sixeight7/VController_v3/VC-mini hardware/Enclosure/VC-mini_lower_cover_b.png

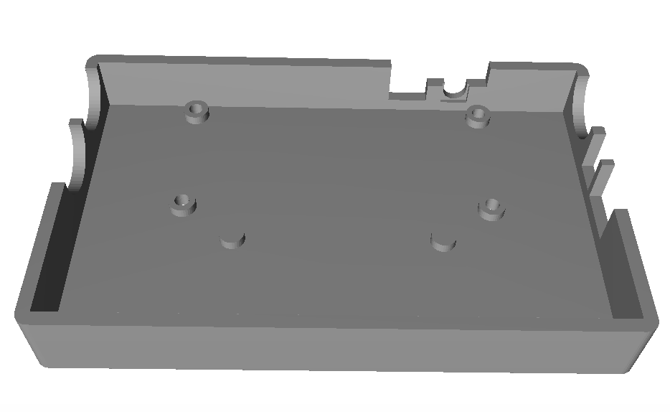
VC-mini hardware/Enclosure/VC-mini_lower_cover_b.png
