sixeight7/VController_v3/VC-touch hardware/Enclosure stl/vctouch_display_bezel.png

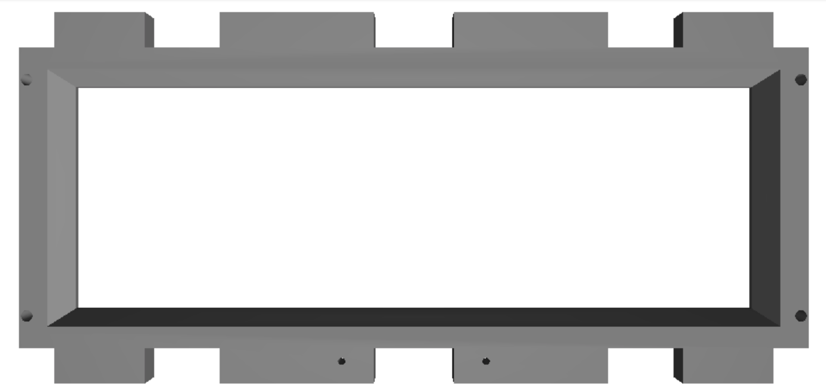
VC-touch hardware/Enclosure stl/vctouch_display_bezel.png
