sixeight7/VController_v3/VController hardware/Enclosure/RPi case/bottom part.png

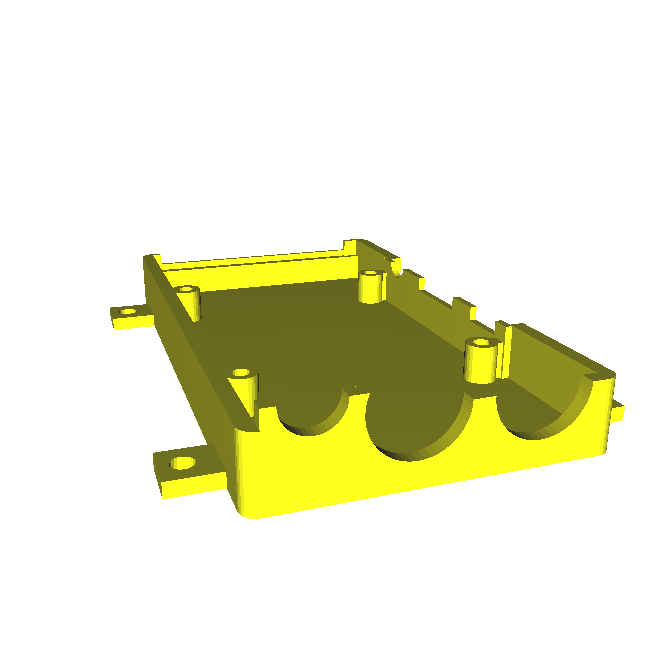
VController hardware/Enclosure/RPi case/bottom part.png
