sixeight7/VController_v3/VController hardware/Enclosure/RPi case/top part.png

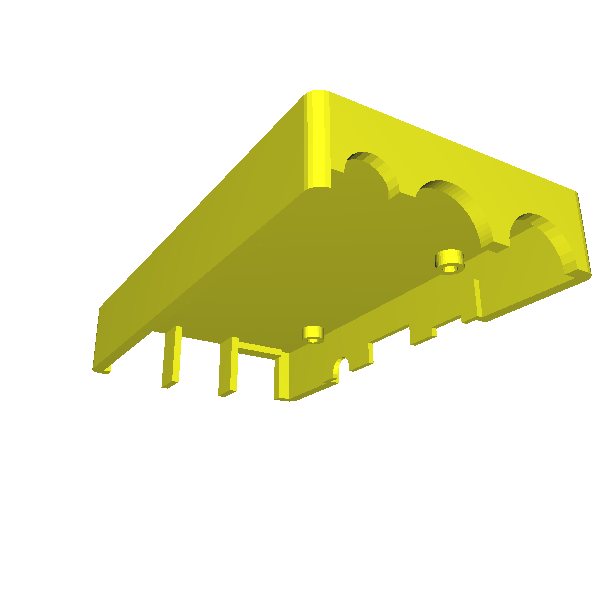
VController hardware/Enclosure/RPi case/top part.png
