sixeight7/VController_v3/VController hardware/Enclosure/3D printing/Large LCD support_2_0.stl

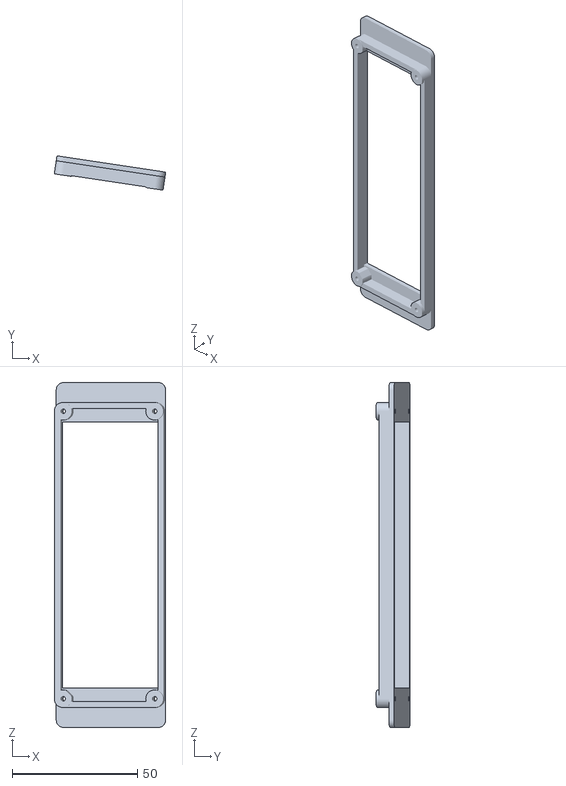
[picture p29: CAD file, 2017-03-23]
VController hardware/Enclosure/3D printing/Large LCD support_2_0.stl
44.6 x 13.7 x 138.0
