sixeight7/VController_v3/VController hardware/Enclosure/3D printing/Small 3xLCD support diameter_2_0.stl

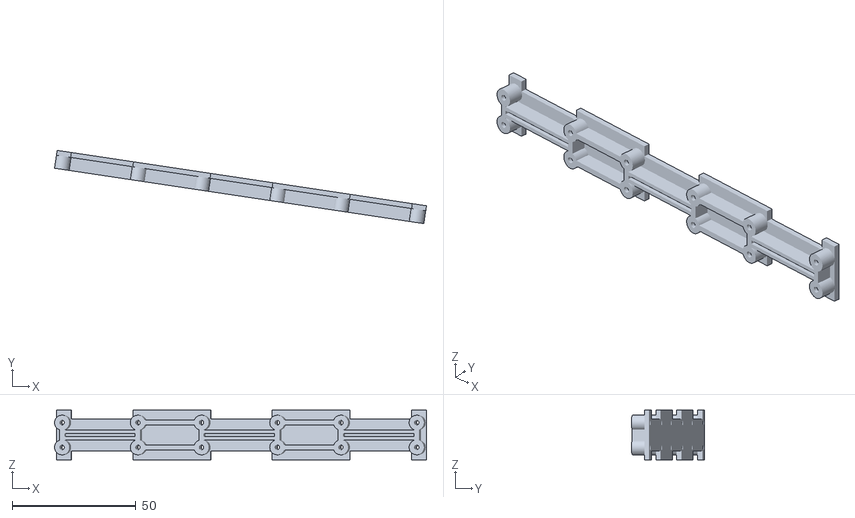
[picture p30: CAD file, 2017-03-23]
VController hardware/Enclosure/3D printing/Small 3xLCD support diameter_2_0.stl
150.4 x 29.6 x 20.2
