sixeight7/VController_v3/VController hardware/Enclosure/Metal/VController_mk4.step

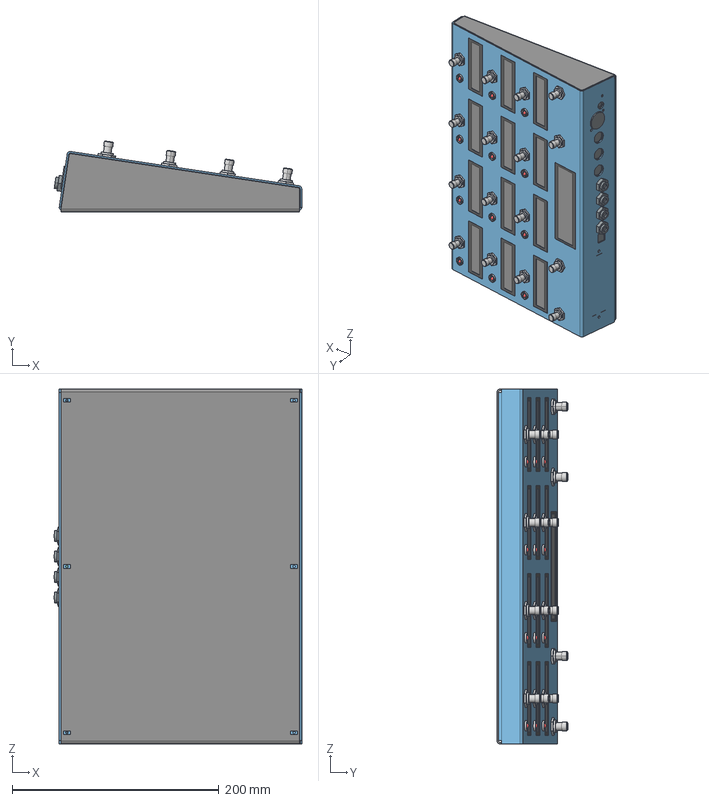
[picture p31: CAD file, 2017-03-23]
VController hardware/Enclosure/Metal/VController_mk4.step
239.2 x 68.7 x 343.0 mm
bracket
rpi_print
LED.9 x 12
houder.1 x 2
houder.2 x 3
print
switch.1.3 x 16
display_small.9 x 12
bottom_plate
top_plate
display_large
houder.5
