sixeight7/VController_v3/VController hardware/Enclosure/3D printing/Half support 3xLCD diameter_2_0.png

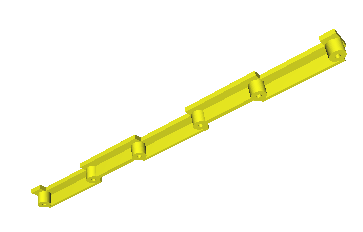
VController hardware/Enclosure/3D printing/Half support 3xLCD diameter_2_0.png
