sixeight7/VController_v3/VController hardware/Enclosure/3D printing/Large LCD support_2_0.png

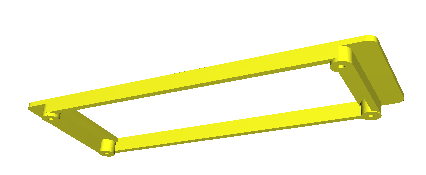
VController hardware/Enclosure/3D printing/Large LCD support_2_0.png
