sixeight7/VController_v3/VController hardware/Enclosure/3D printing/Small 3xLCD support Adafruit.png

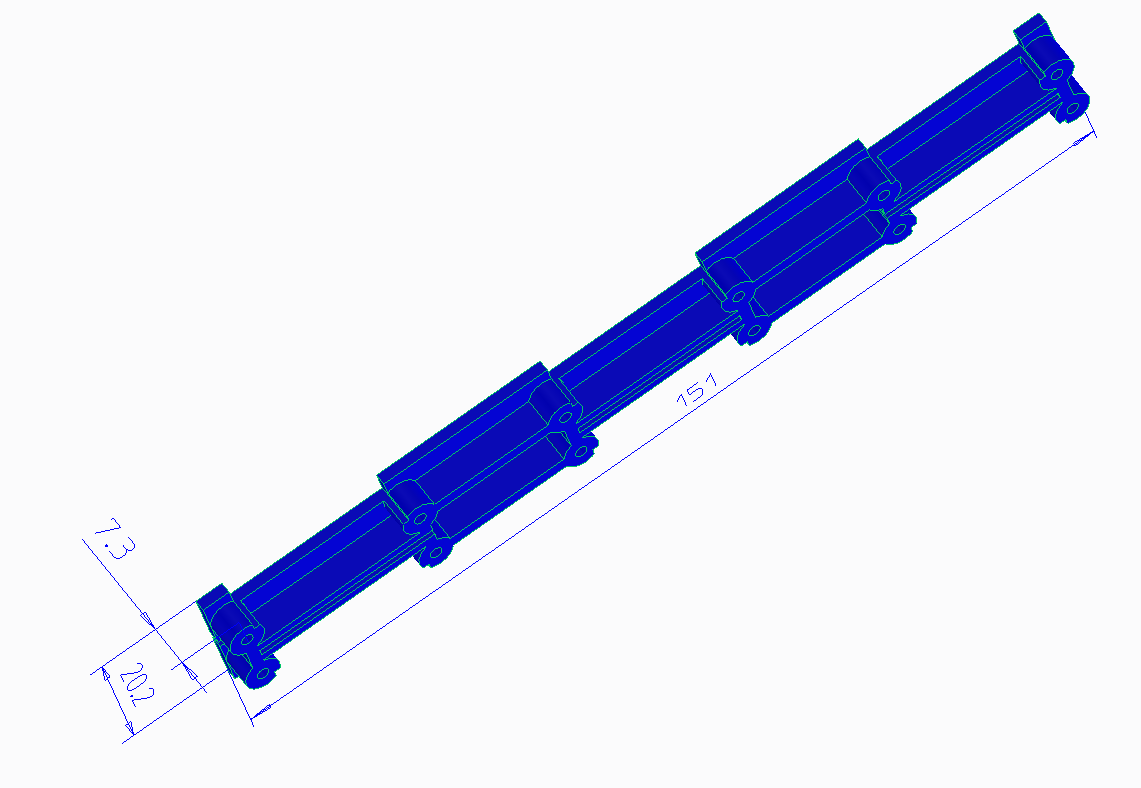
VController hardware/Enclosure/3D printing/Small 3xLCD support Adafruit.png
