sixeight7/VController_v3/VController hardware/Display board/VController display board PCB.pdf

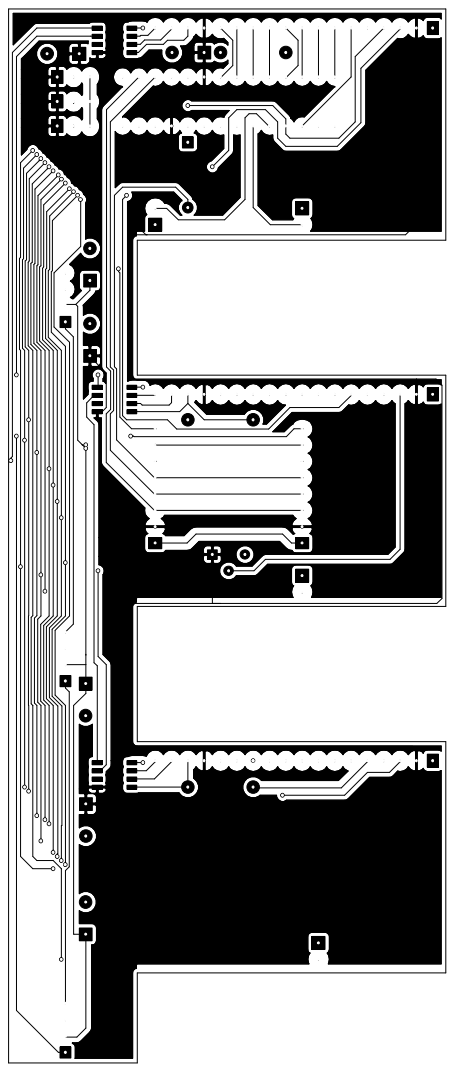
[picture p96: page 1]

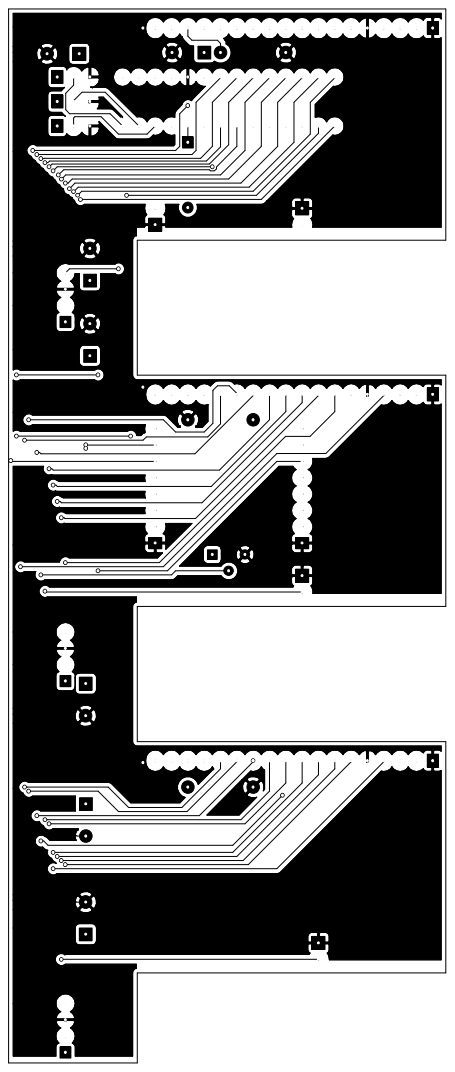
[picture p97: page 2]

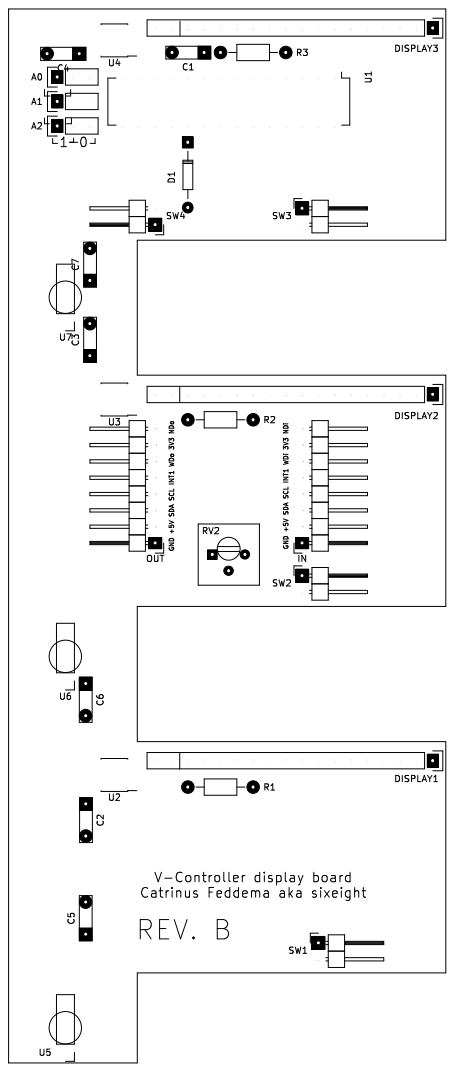
[picture p98: page 3]
