sixeight7/VController_v3/VController hardware/Display board/VController Display Board.pdf

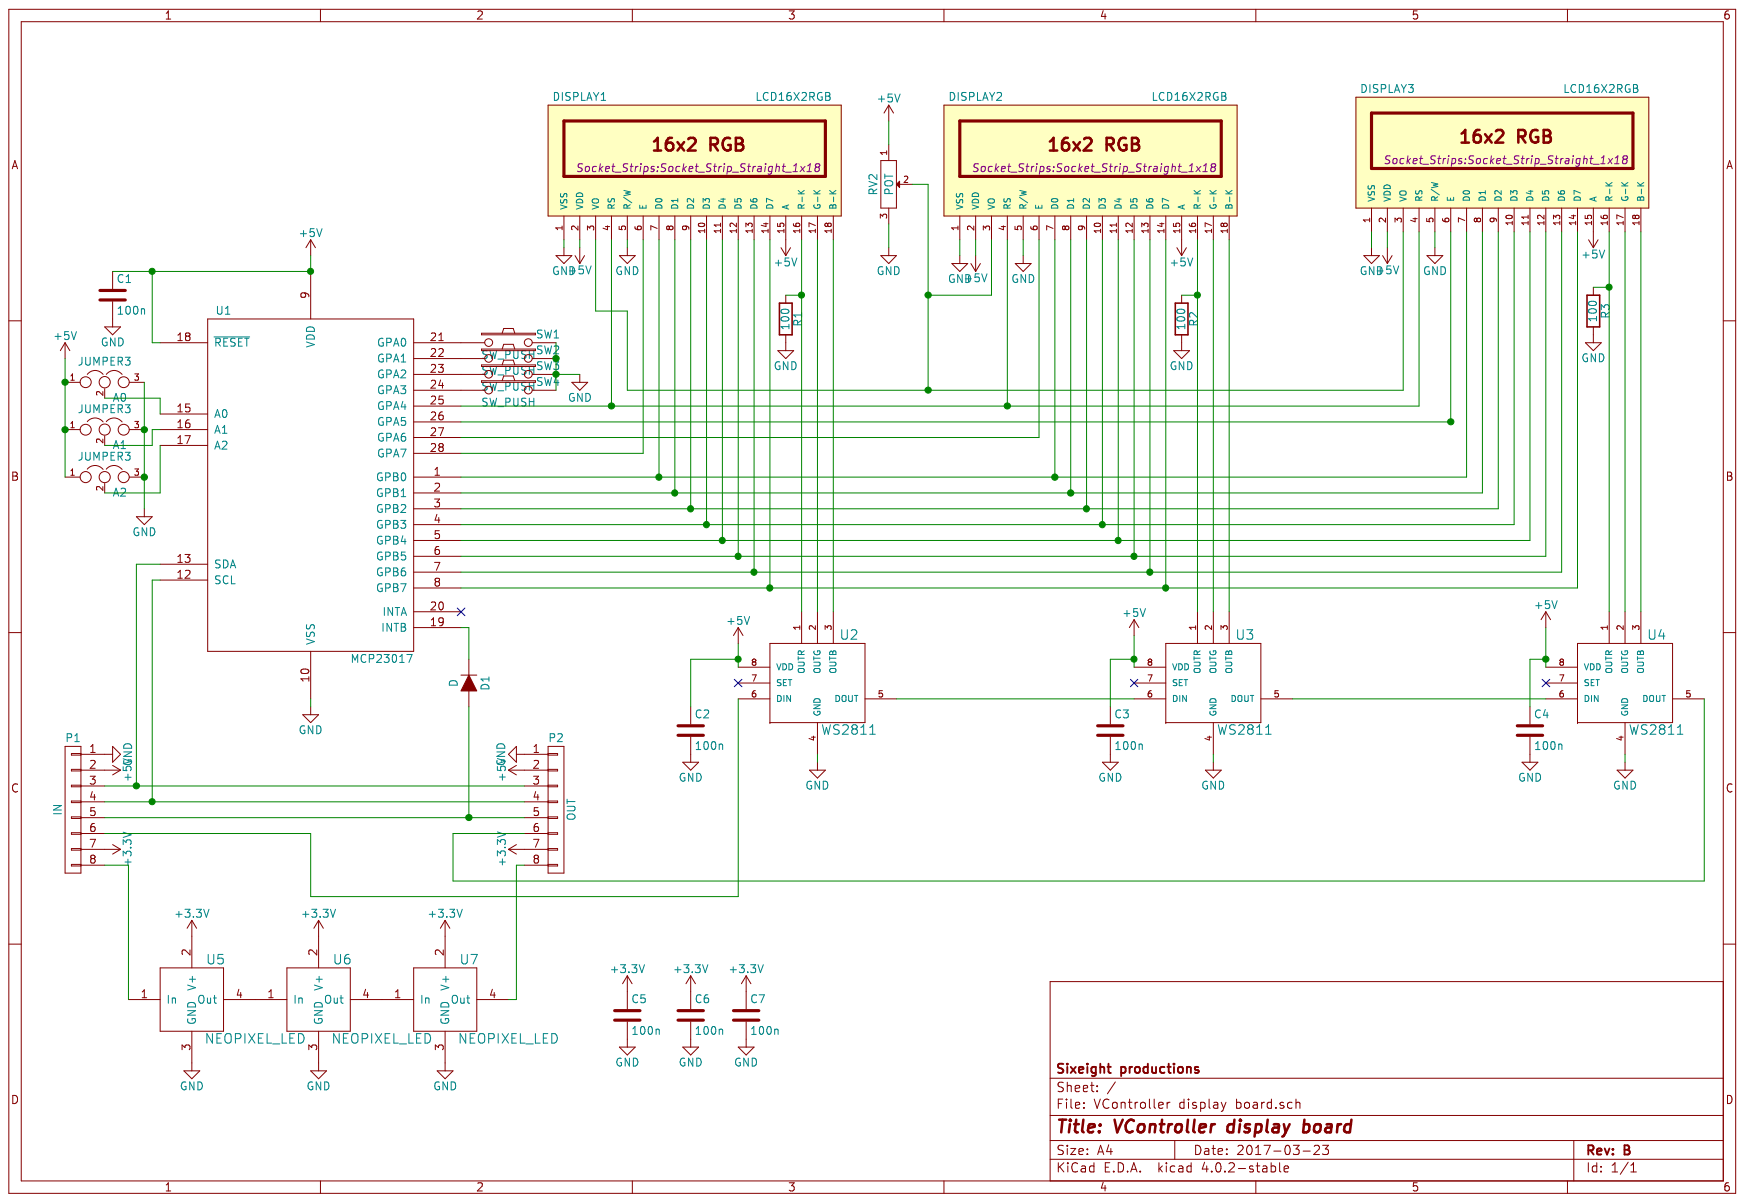
[picture p99: page 1]
