sixeight7/VController_v3/VController hardware/Enclosure/Metal/RPi expansion board bracket.pdf

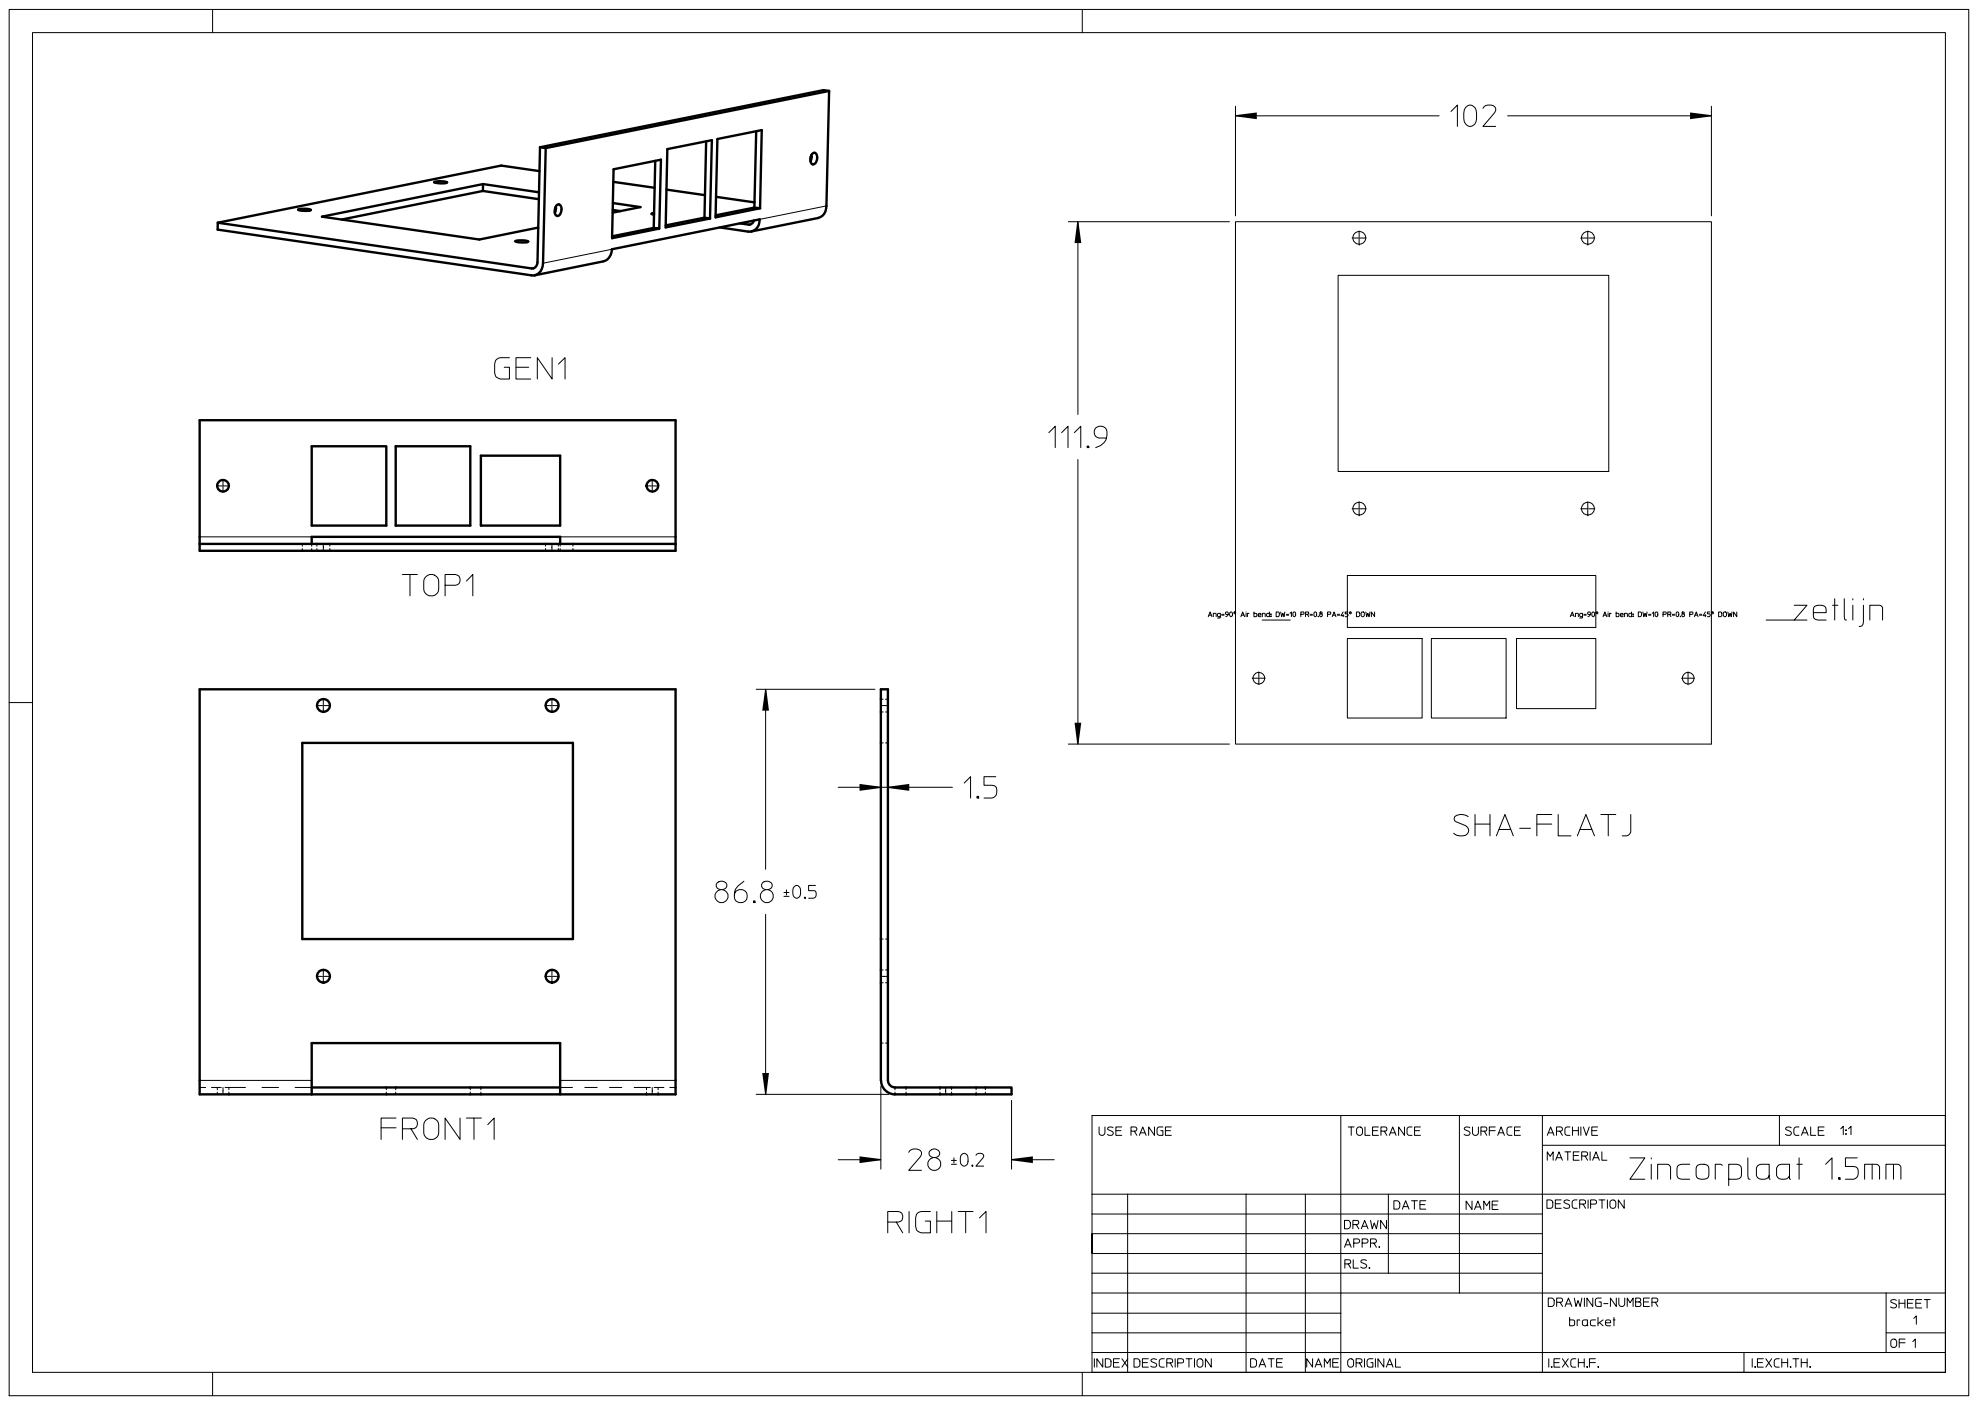
[picture p100: page 1]
