sixeight7/VController_v3/VController hardware/Enclosure/Metal/top plate VController Adafruit displays.pdf

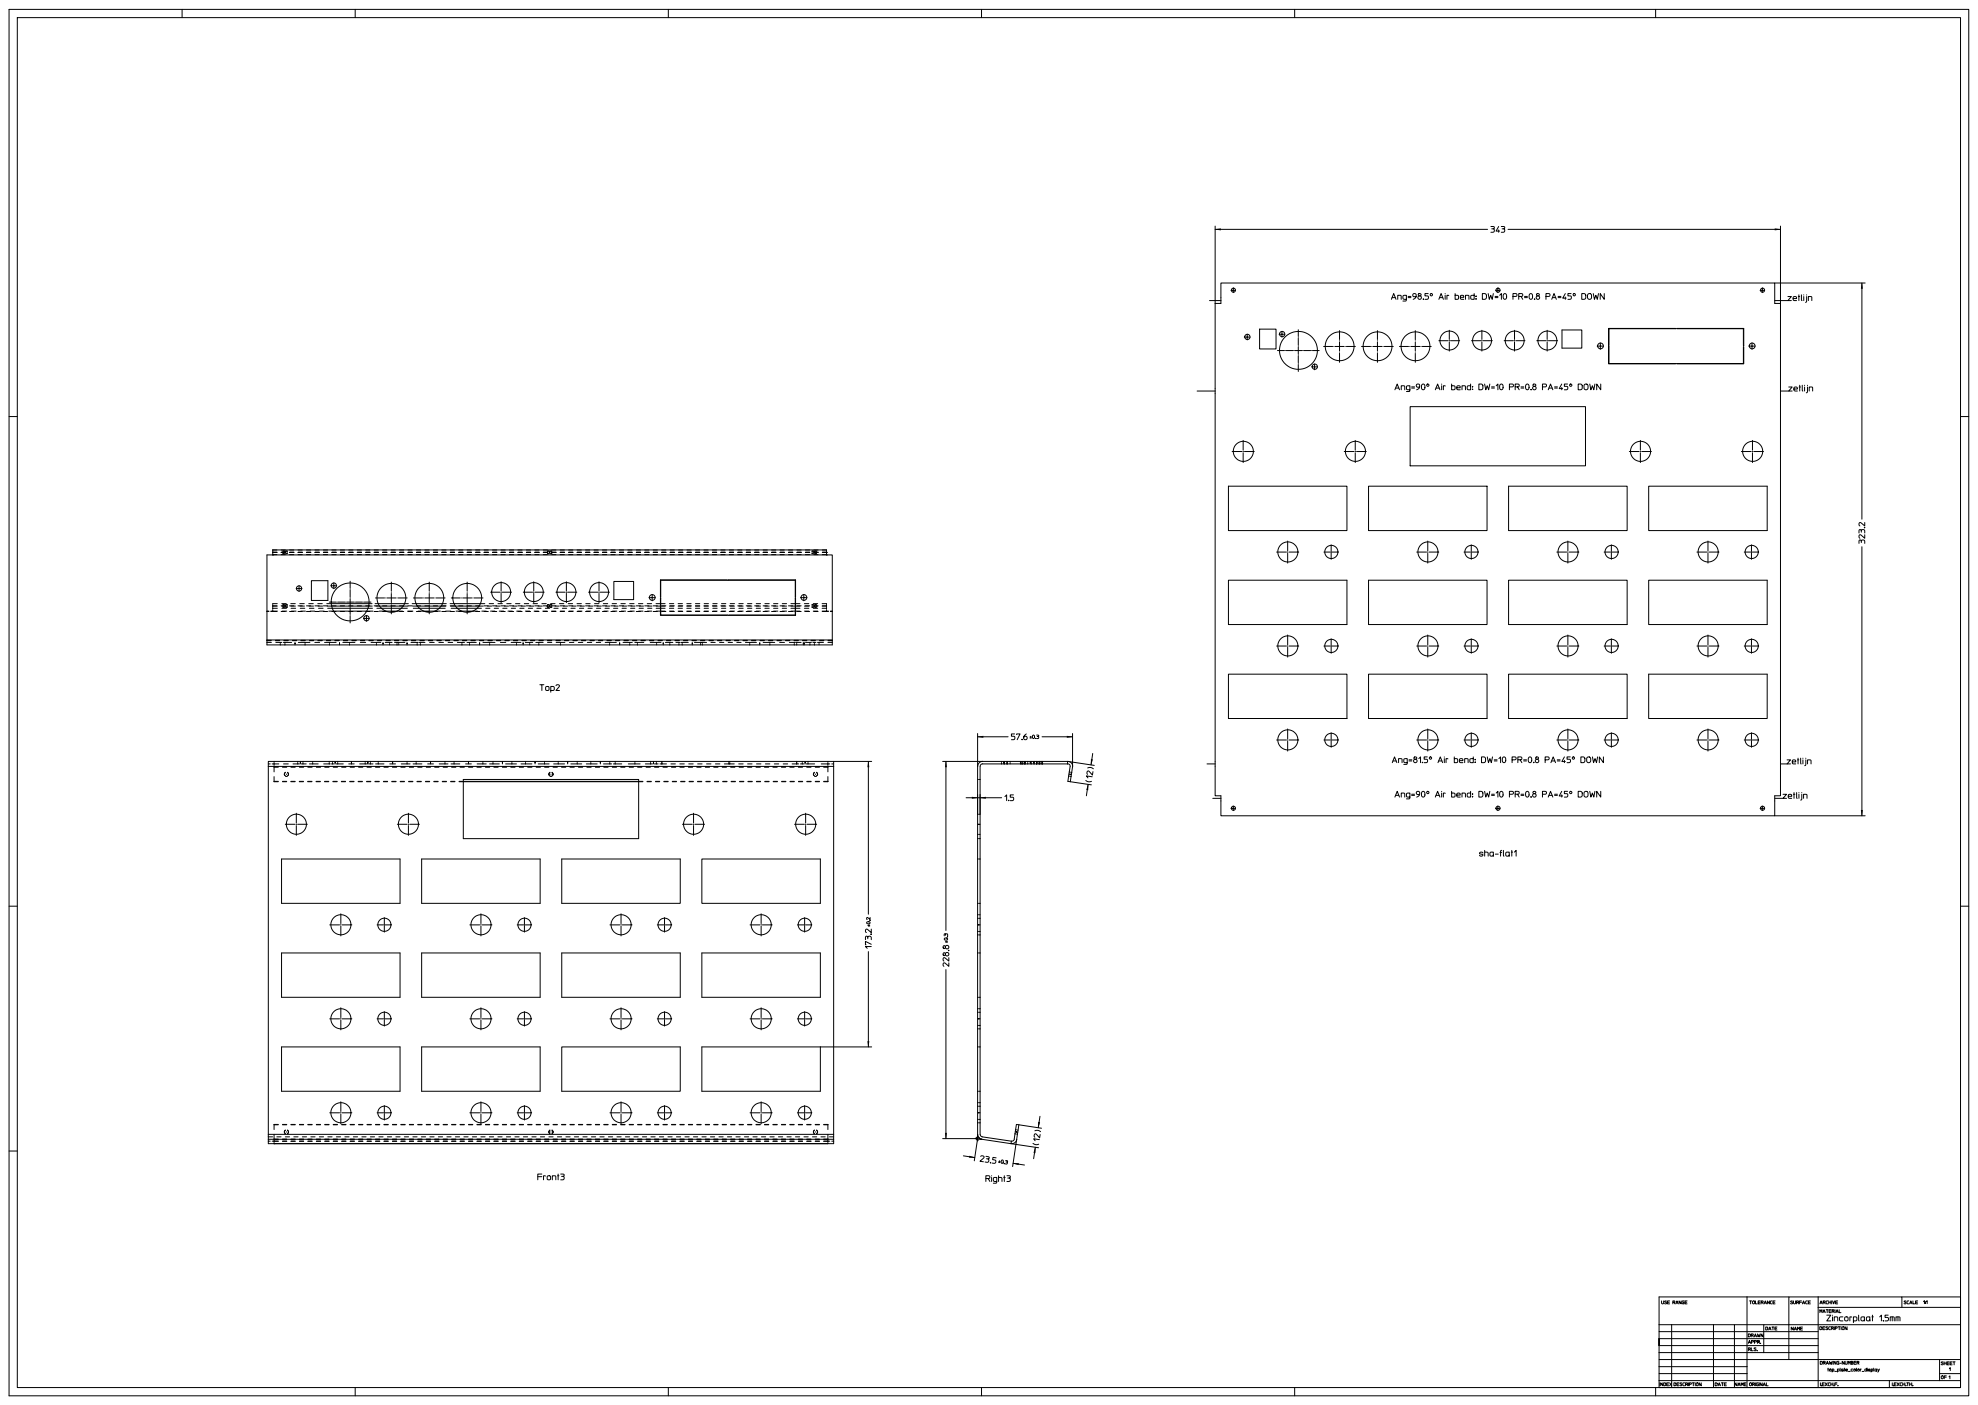
[picture p101: page 1]
