sixeight7/VController_v3/VController hardware/Enclosure/Perspex/perspex.pdf

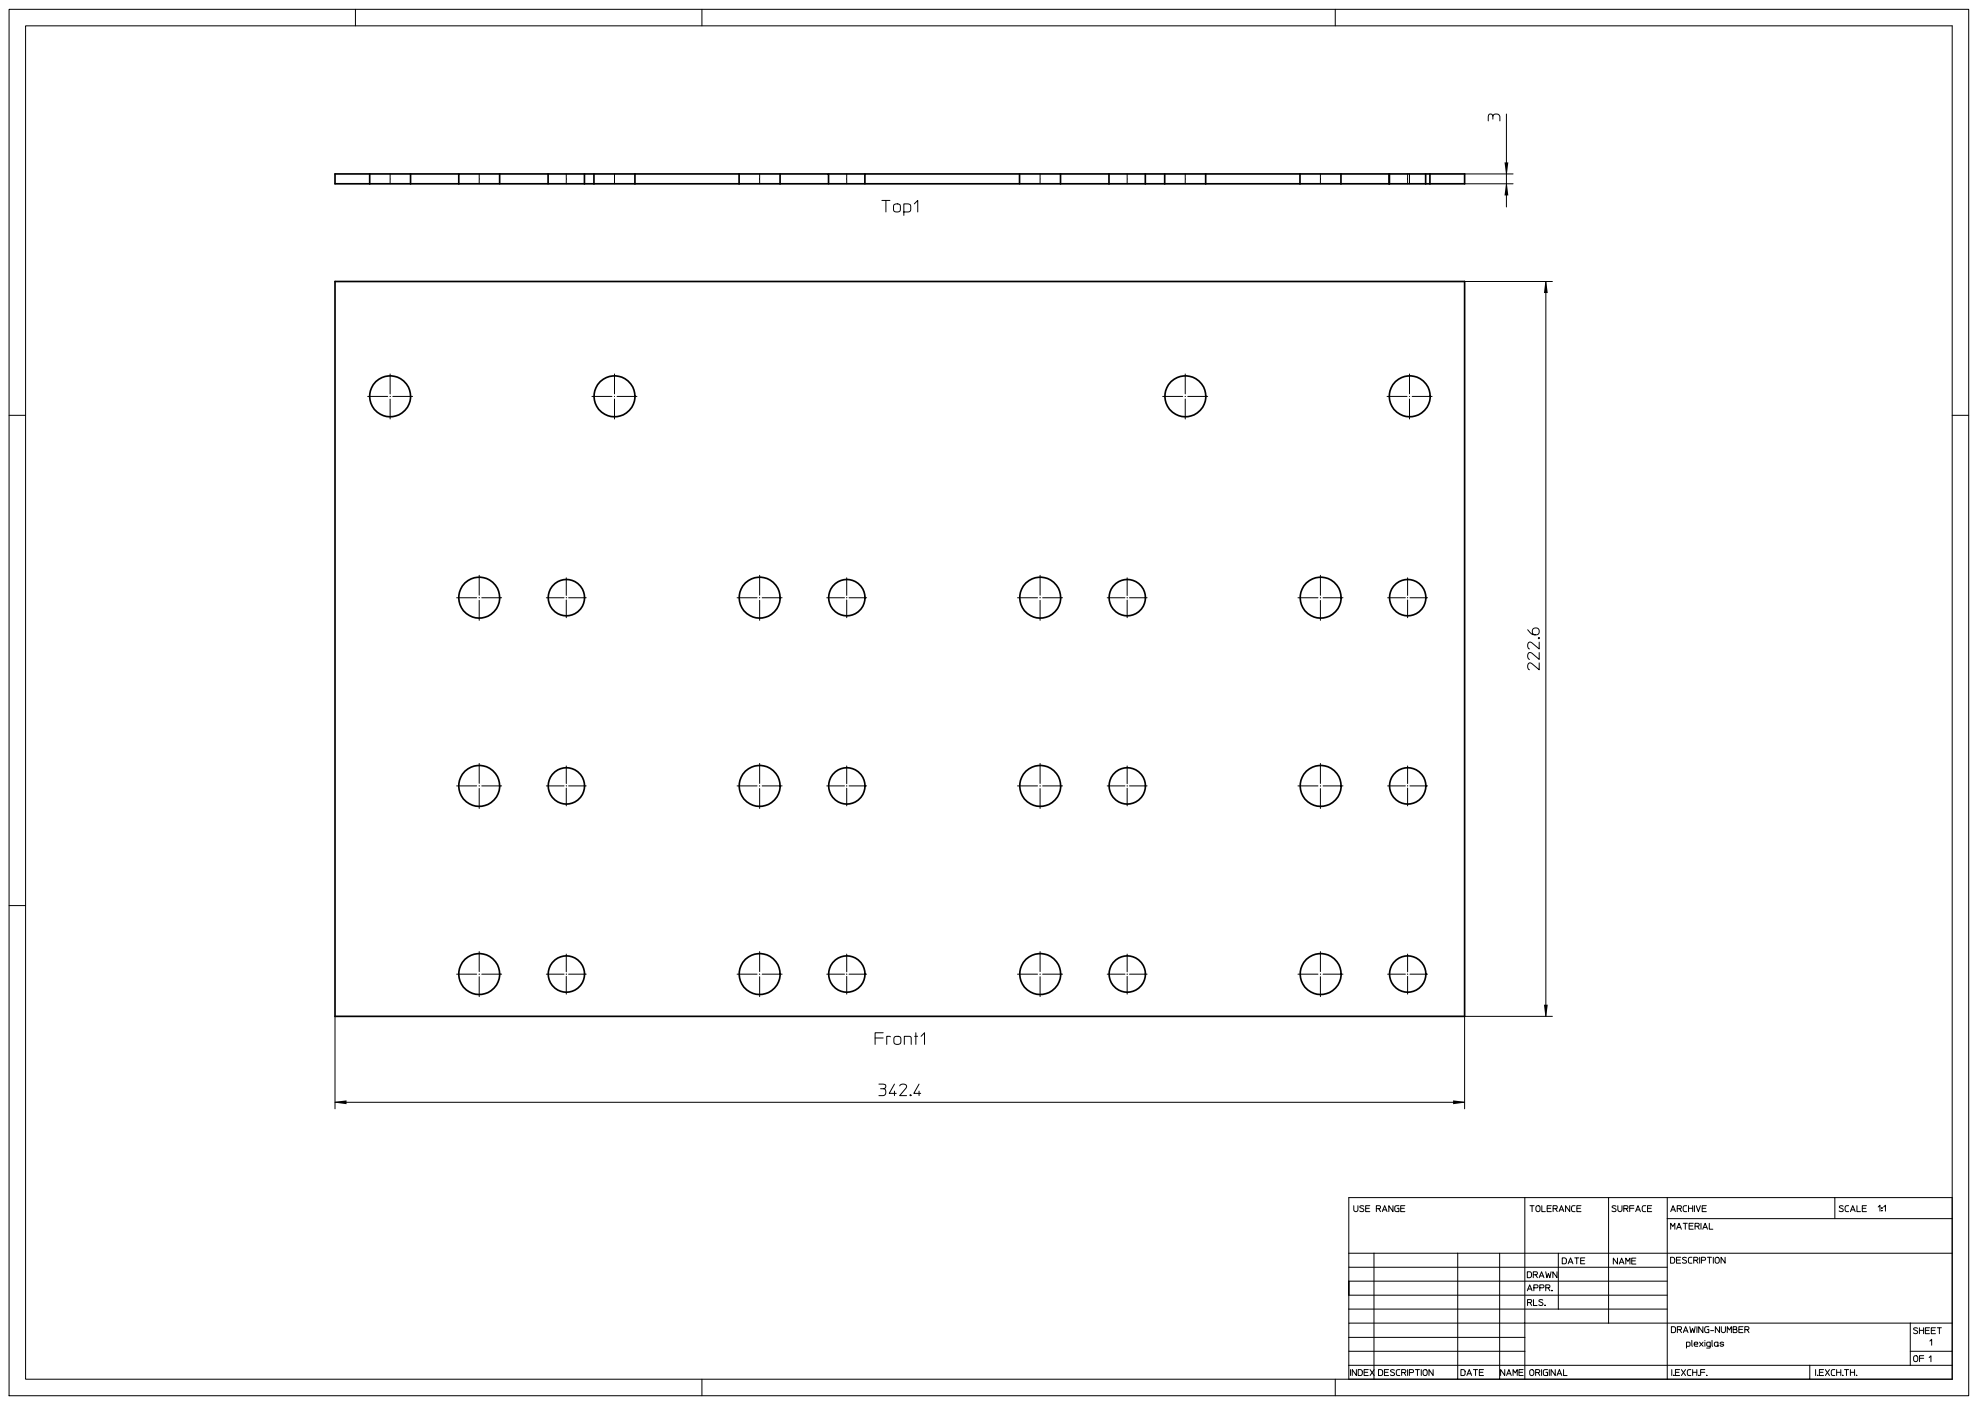
[picture p102: page 1]
