sixeight7/VController_v3/VController hardware/Enclosure/Metal/bottom plate VController_mk4_05122016.pdf

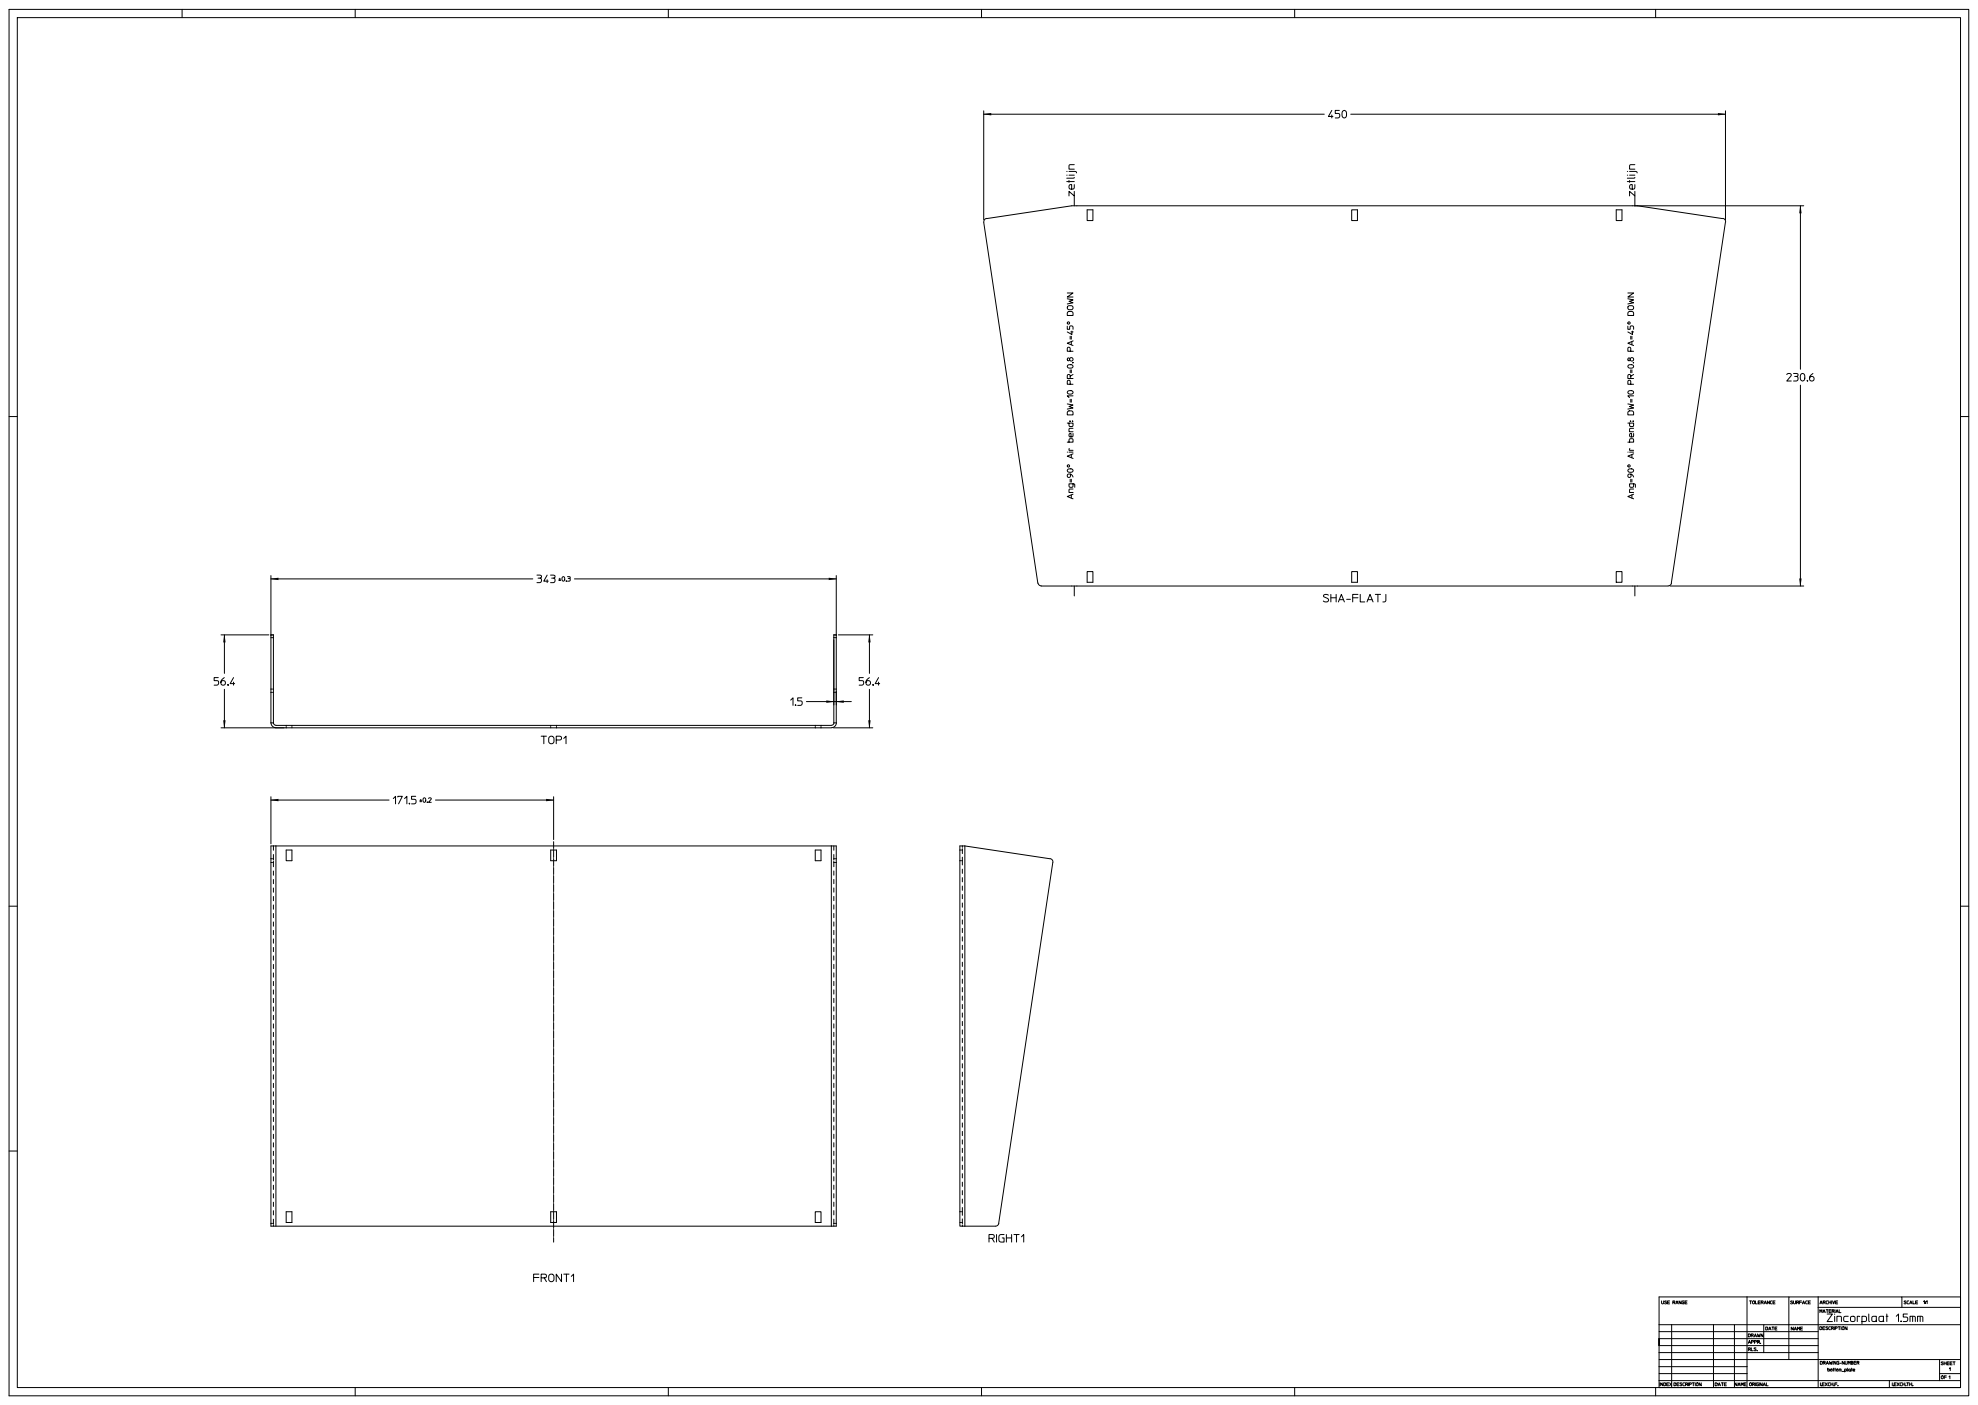
[picture p103: page 1]
