sixeight7/VController_v3/VController hardware/Enclosure/Metal/top plate VController_mk4_05122016.pdf

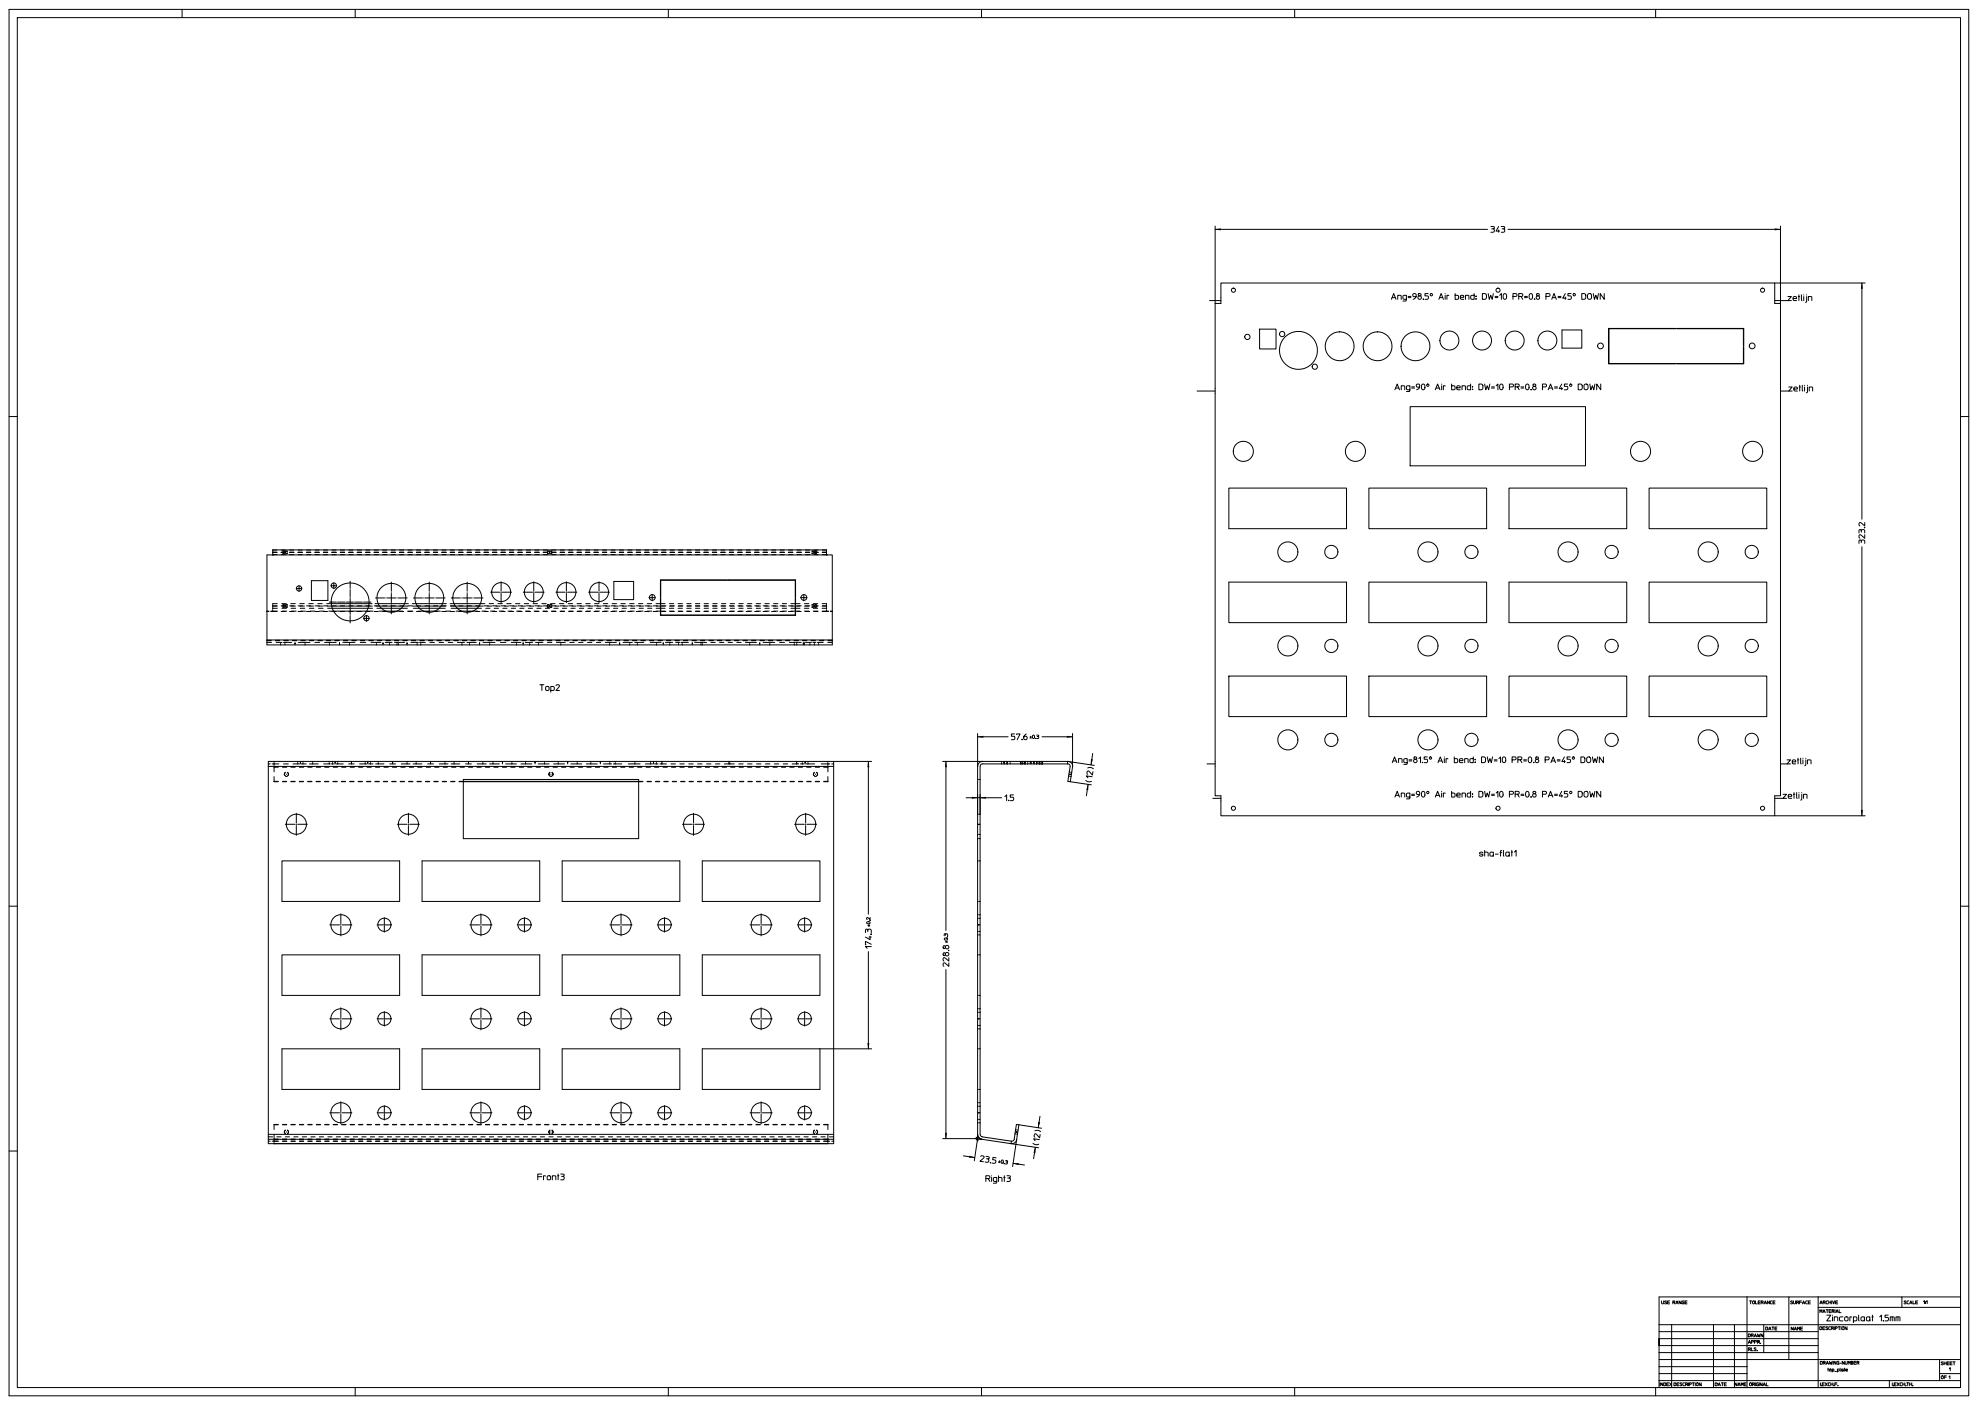
[picture p104: page 1]
