sixeight7/VController_v3/RPi Expansion Board/RPi Expansion Board PCB.pdf

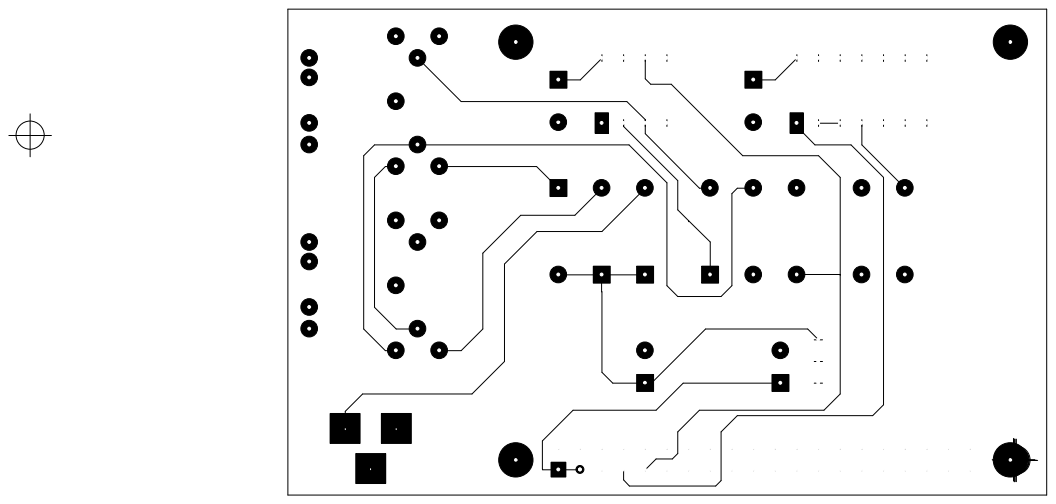
[picture p105: page 1]

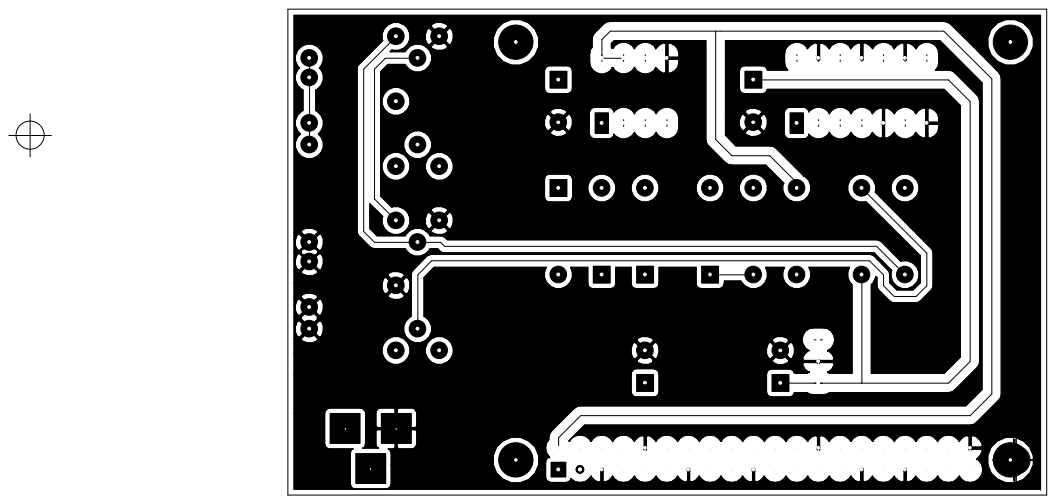
[picture p106: page 2]

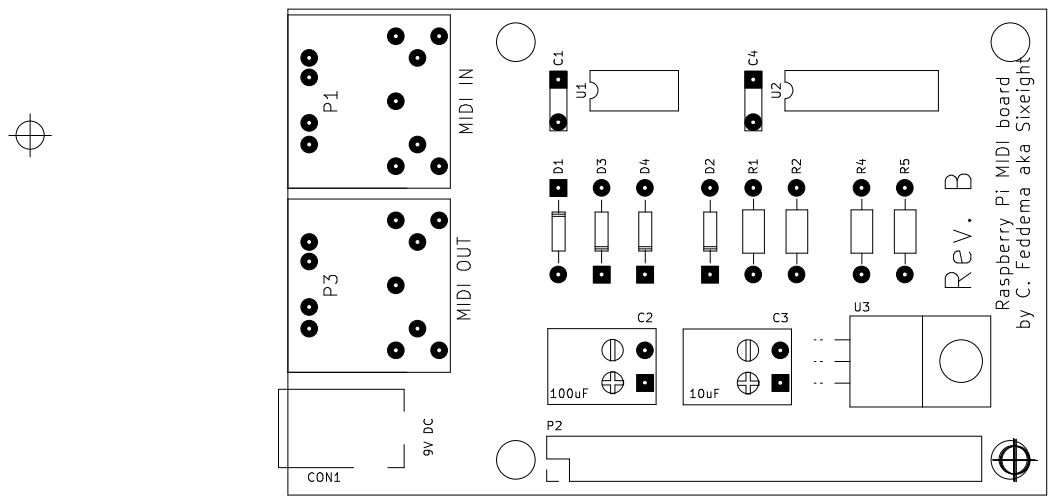
[picture p107: page 3]
