sixeight7/VController_v3/RPi Expansion Board/RPi expansion board.pdf

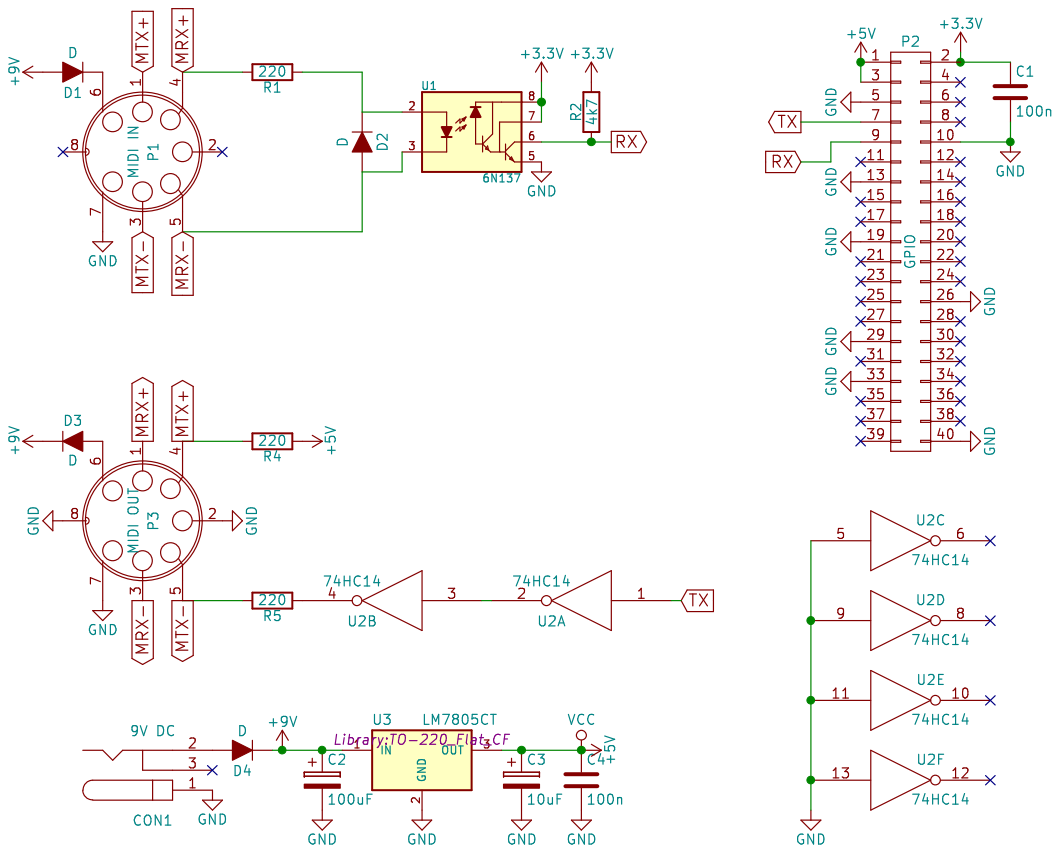
[picture p108: page 1]
