sixeight7/VController_v3/Firmware/VC-edit/VController/config.h

#define CONFIG_H
#include <QApplication>
#include <QVector>
struct Cmd_struct
{
    uint8_t Page;   // The page this command belongs to
    uint8_t Switch; // The switch this command belongs to
    uint8_t Type;   // The type of command
    uint8_t Device; // The device for this command (can be device number, CURRENT or COMMON)
    uint8_t Data1;  // Can be the patch/parameter/assign/pc/cc/note or page number
    uint8_t Data2;  // Can be bank number of parameter/cc type
    uint8_t Value1; // Values for parameters, etc.
    uint8_t Value2;
    uint8_t Value3;
    uint8_t Value4;
    bool operator==(const Cmd_struct &other) const // In C++, structs do not have a comparison operator generated by default. You need to write your own
    {
        return Page == other.Page && Switch == other.Switch && Type == other.Type && Device == other.Device && Data1 == other.Device
                && Data2 == other.Data2 && Value1 == other.Value1 && Value2 == other.Value2 && Value3 == other.Value3 && Value4 == other.Value4;
    }
};
#define GP10 0
#define GR55 1
#define VG99 2
#define ZG3 3
#define ZMS70 4
#define M13 5
#define HLX 6
#define AXEFX 7
#define KTN 8
#define KPA 9
#define SVL 10
#define SY1000 11
#define GM2 12
#define MG300 13
#define NUMBER_OF_PROGRAMMED_DEVICES 14
#define USER1 14
#define USER2 15
#define USER3 16
#define USER4 17
#define USER5 18
#define USER6 19
#define USER7 20
#define USER8 21
#define USER9 22
#define USER10 23
#define NUMBER_OF_USER_DEVICES 10
#define NUMBER_OF_DEVICES (NUMBER_OF_PROGRAMMED_DEVICES + NUMBER_OF_USER_DEVICES)
#define CURRENT 254 // To select the current device
#define COMMON 255 // Not really a device, but used for common procedures, that are not device specific or for all devices.
#define LABEL 0xE0 // Bit 6 - 8 of the switch number is set to one all labels - this saved one byte and keeps the command structure short.
#define ON_DUAL_PRESS 0x80 // Switch and right neighbouring switch are pressed
#define ON_LONG_PRESS 0x40
#define ON_RELEASE 0x20
#define SWITCH_MASK 0x1F
#define SWITCH_TYPE_MASK 0xE0
#define NUMBER_OF_COMMON_TYPES 13 // Only the one that can be selected in the command builder
#define NOTHING 0           // Example: {<PAGE>, <SWITCH>, NOTHING, COMMON}
#define PAGE 1              // Example: {<PAGE>, <SWITCH>, PAGE, COMMON, SELECT, PAGE_COMBO1}
#define TAP_TEMPO 2         // Example: {<PAGE>, <SWITCH>, TAP_TEMPO, COMMON}
#define SET_TEMPO 3         // Example: {<PAGE>, <SWITCH>, SET_TEMPO, COMMON, 120}
#define GLOBAL_TUNER 4      // Example: {<PAGE>, <SWITCH>, GLOBAL_TUNER, COMMON}
#define MIDI_PC 5           // Example: {<PAGE>, <SWITCH>, MIDI_PC, COMMON, Program, Channel, Port}
#define MIDI_CC 6           // Example: {<PAGE>, <SWITCH>, MIDI_CC, COMMON, Controller, CC_TOGGLE_TYPE, Value1, Value2, Channel, Port}
#define MIDI_NOTE 7         // Example: {<PAGE>, <SWITCH>, MIDI_NOTE, COMMON, Note, Velocity, Channel, Port}
#define SELECT_NEXT_DEVICE 8// Example: {<PAGE>, <SWITCH>, SELECT_NEXT_DEVICE, COMMON}
#define SETLIST 9            // Example: {<PAGE>, <SWITCH>, SETLIST, COMMON, NEXT}
#define SONG 10              // Example: {<PAGE>, <SWITCH>, SONG, COMMON, NEXT}
#define MODE 11              // Example: {<PAGE>, <SWITCH>, MODE, COMMON, SELECT, 0}
#define MIDI_MORE 12         // Example: {<PAGE>, <SWITCH>, MIDI_PC, COMMON, START}
#define NUMBER_OF_COMMON_TYPES_NOT_SELECTABLE 1
#define MENU 13             // Example: {<PAGE>, <SWITCH>, MENU, COMMON, 1} - to display first menu item
#define NUMBER_OF_DEVICE_TYPES 10
#define PATCH 100      // Example: {<PAGE>, <SWITCH>, PATCH, <DEVICE>, 25, 1} - to select patch 125
#define PARAMETER 101      // Example: {<PAGE>, <SWITCH>, PARAMETER, <DEVICE>, 1, TOGGLE, 1, 0}
#define ASSIGN 102         // Example: {<PAGE>, <SWITCH>, ASSIGN, <DEVICE>, SELECT, 1, 21}
#define SNAPSCENE 103      // Example: {<PAGE>, <SWITCH>, SNAPSCENE, <DEVICE>, 1}
#define LOOPER 104         // Example: {<PAGE>, <SWITCH>, LOOPER, <DEVICE>, START}
#define MUTE 105           // Example: {<PAGE>, <SWITCH>, MUTE, <DEVICE>}
#define OPEN_PAGE_DEVICE 106     // Example: {<PAGE>, <SWITCH>, OPEN_PAGE_DEVICE, ZG3, PAGE_ZOOM_PATCH_BANK}
#define OPEN_NEXT_PAGE_OF_DEVICE 107      // Example: {<PAGE>, <SWITCH>, OPEN_NEXT_PAGE_OF_DEVICE, <DEVICE>}
#define MASTER_EXP_PEDAL 108 // Example: {<PAGE>, <SWITCH>, MASTER_EXP_PEDAL, <DEVICE>, <number>} number of expression pedal: 0, 1, 2 or 3. If 0, it will choose the number as selected with TOGGLE_EXP_PEDAL
#define TOGGLE_EXP_PEDAL 109 // Example: {<PAGE>, <SWITCH>, TOGGLE_EXP_PEDAL, <DEVICE>}
#define NUMBER_OF_DEVICE_TYPES_NOT_SELECTABLE 6
#define DIRECT_SELECT 110  // Example: {<PAGE>, <SWITCH>, DIRECT_SELECT, <DEVICE>, 1, 10}
#define PAR_BANK 111       // Example: {<PAGE>, <SWITCH>, PAR_BANK, <DEVICE>, 1, 10}
#define PAR_BANK_UP 112    // Example: {<PAGE>, <SWITCH>, PAR_BANK_UP, <DEVICE>, 10}
#define PAR_BANK_DOWN 113  // Example: {<PAGE>, <SWITCH>, PAR_BANK_DOWN, <DEVICE>, 10}
#define PAR_BANK_CATEGORY 114   // Example: {<PAGE>, <SWITCH>, PAR_BANK_CATEGORY, <DEVICE>, 1}
#define SAVE_PATCH 115    // Example: {<PAGE>, <SWITCH>, TOGGLE_EXP_PEDAL, <DEVICE>}
#define SELECT 0           // Example: {<PAGE>, <SWITCH>, PAGE, COMMON, SELECT, PAGE_COMBO1}
#define BANKSELECT 1      // Example: {<PAGE>, <SWITCH>, PAGE, COMMON, BANKSELECT, 1, 10} - to select the first item in a bank of 10
#define BANKUP 2          // Example: {<PAGE>, <SWITCH>, PAGE, COMMON, BANKUP, 10}
#define BANKDOWN 3        // Example: {<PAGE>, <SWITCH>, PAGE, COMMON, BANKDOWN, 10}
#define NEXT 4             // Example: {<PAGE>, <SWITCH>, PAGE, COMMON, NEXT}
#define PREV 5             // Example: {<PAGE>, <SWITCH>, PAGE, COMMON, PREV}
#define NUMBER_OF_SELECT_TYPES 6
#define SONG_MODE 0
#define PAGE_MODE 1
#define DEVICE_MODE 2
#define NUMBER_OF_MODES 3
#define MOMENTARY 0
#define TOGGLE 1
#define TRISTATE 2
#define FOURSTATE 3
#define STEP 4 // Set minimum ,maximum and step value
#define RANGE 5 // For use with expression pedal
#define UPDOWN 6 // Press and hold to increase/decrease. Press shortly to change direction
#define ONE_SHOT 7
#define TGL_OFF 255 // To show nothing
#define MUTE_ON 0
#define MUTE_OFF 1
#define MUTE_OFF_AND_ALWAYS_ON_TOGGLE 2
#define MUTE_TOGGLE 3
#define TIME_2000 255 // For delay times up to 2000 ms
#define TIME_1000 254 // For delay times up to 1000 ms
#define TIME_500 253 // For pre delay times up to 500 ms
#define TIME_300 252 // For pre delay times up to 300 ms
#define CC_ONE_SHOT 0 // Send a single CC message on press
#define CC_MOMENTARY 1 // Send first message on press, second on release
#define CC_TOGGLE 2 // Default state off - send message 1 on first press, second message on second press
#define CC_TOGGLE_ON 3 // Default state on - send message 2 on first press, first message on second press
#define CC_RANGE 4 // For use with expression pedal
#define CC_STEP 5 // Step through the values from minimum to maximum
#define CC_UPDOWN 6 // Press and hold to increase/decrease. Press shortly to change direction
#define MIDI_START 0
#define MIDI_STOP 1
#define MIDI_START_STOP 2
#define SL_SELECT 0
#define SL_BANKSELECT 1
#define SL_BANKUP 2
#define SL_BANKDOWN 3
#define SL_PREV 4
#define SL_NEXT 5
#define SL_EDIT 6
#define SETLIST_TARGET_SONG 0
#define SETLIST_TARGET_PAGE 1
#define SETLIST_TARGET_FIRST_DEVICE 2
#define SONG_SELECT 0
#define SONG_BANKSELECT 1
#define SONG_BANKUP 2
#define SONG_BANKDOWN 3
#define SONG_PREV 4
#define SONG_NEXT 5
#define SONG_PARTSEL 6
#define SONG_EDIT 7
#define SONG_PREVNEXT_SONG 0 // PREV and NEXT will choose previous or next song
#define SONG_PREVNEXT_PART 1 // PREV and NEXT will choose previous or next part
#define SONG_PREVNEXT_SONGPART 2  // PREV and NEXT will choose previous or next part and move to the next song
#define SONG_TARGET_OFF 0
#define SONG_TARGET_PC 1
#define SONG_TARGET_CC 2
#define SONG_TARGET_TEMPO 3
#define SONG_TARGET_FIRST_DEVICE 4
#define NUMBER_OF_LOOPER_TYPES 11
#define LOOPER_SHOW_HIDE 1
#define LOOPER_PLAY_STOP 2
#define LOOPER_REC_OVERDUB 3
#define LOOPER_UNDO_REDO 4
#define LOOPER_HALF_SPEED 5
#define LOOPER_REVERSE 6
#define LOOPER_PLAY_ONCE 7
#define LOOPER_PRE_POST 8
#define LOOPER_REC_PLAY_OVERDUB 9 // KPA looper option
#define LOOPER_STOP_ERASE 10 // KPA looper option
#define USBMIDI_PORT 0x00
#define MIDI1_PORT 0x10
#define MIDI2_PORT 0x20
#define MIDI3_PORT 0x30
#define MIDI4_PORT 0x40
#define USBHMIDI_PORT 0x50
#define MIDI5_PORT 0x60
#define ALL_MIDI_PORTS 0xF0
#define FC300_CTL1 ASSIGN, VG99, SELECT, 0, 1
#define FC300_CTL2 ASSIGN, VG99, SELECT, 1, 2
#define FC300_CTL3 ASSIGN, VG99, SELECT, 2, 3
#define FC300_CTL4 ASSIGN, VG99, SELECT, 3, 4
#define FC300_CTL5 ASSIGN, VG99, SELECT, 4, 5
#define FC300_CTL6 ASSIGN, VG99, SELECT, 5, 6
#define FC300_CTL7 ASSIGN, VG99, SELECT, 6, 7
#define FC300_CTL8 ASSIGN, VG99, SELECT, 7, 8
#define FC300_EXP1 ASSIGN, VG99, SELECT, 8, 9
#define FC300_EXP_SW1 ASSIGN, VG99, SELECT, 9, 10
#define FC300_EXP2 ASSIGN, VG99, SELECT, 10, 11
#define FC300_EXP_SW2 ASSIGN, VG99, SELECT, 11, 12
#define MENU_SELECT 255
#define MENU_BACK 254
#define MENU_SET_VALUE 253
#define MENU_PREV 252
#define MENU_NEXT 251
#define FIRST_FIXED_CMD_PAGE_VC 201
#define FIRST_SELECTABLE_FIXED_CMD_PAGE_VC 203
#define PAGE_VC_MENU 201
#define PAGE_VC_CURRENT_DIRECT_SELECT 202
#define PAGE_VC_DEVICE_MODE 203
#define PAGE_VC_PAGE_MODE 204
#define PAGE_VC_CURRENT_PATCH_BANK 205
#define PAGE_VC_GR55_PATCH_BANK 206
#define PAGE_VC_ZOOM_PATCH_BANK 207
#define PAGE_VC_CURRENT_PARAMETER 208
#define PAGE_VC_GP10_ASSIGNS 209
#define PAGE_VC_GR55_ASSIGNS 210
#define PAGE_VC_VG99_EDIT 211
#define PAGE_VC_VG99_ASSIGNS 212
#define PAGE_VC_VG99_ASSIGNS2 213
#define PAGE_VC_M13_PARAMETER 214
#define PAGE_VC_FULL_LOOPER 215
#define PAGE_VC_HLX_PATCH_BANK 216
#define PAGE_VC_HLX_PARAMETER 217
#define PAGE_VC_SNAPSCENE_LOOPER 218
#define PAGE_VC_KTN_PATCH_BANK 219
#define PAGE_VC_KTN_EDIT 220
#define PAGE_VC_KTN_FX 221
#define PAGE_VC_KPA_RIG_SELECT 222
#define PAGE_VC_KPA_FX_CONTROL 223
#define PAGE_VC_KPA_LOOPER 224
#define PAGE_VC_CURRENT_ASSIGN 225
#define PAGE_VC_SY1000_PATCH_BANK 226
#define PAGE_VC_SY1000_ASSIGNS 227
#define PAGE_VC_SY1000_SCENES 228
#define PAGE_VC_MG300_PATCH_BANK 229
#define PAGE_VC_SONG_MODE 230
#define PAGE_VC_SONG_SELECT 231
#define PAGE_VC_SETLIST_SELECT 232
#define PAGE_VC_USER_PATCH_BANK 233
#define PAGE_VC_USER_PAR_BANK 234
#define PAGE_VC_USER_SCENES 235
#define LAST_FIXED_CMD_PAGE_VC 235
#define DEFAULT_VC_PAGE PAGE_VC_SELECT // The page that gets selected when a valid page number is unknown
#define FAS_DEFAULT_VC_PAGE1 PAGE_VC_CURRENT_PATCH_BANK
#define FAS_DEFAULT_VC_PAGE2 PAGE_VC_CURRENT_PARAMETER
#define FAS_DEFAULT_VC_PAGE3 PAGE_VC_SNAPSCENE_LOOPER
#define FAS_DEFAULT_VC_PAGE4 0
#define GP10_DEFAULT_VC_PAGE1 PAGE_VC_CURRENT_PATCH_BANK
#define GP10_DEFAULT_VC_PAGE2 PAGE_VC_CURRENT_PARAMETER
#define GP10_DEFAULT_VC_PAGE3 PAGE_VC_GP10_ASSIGNS
#define GP10_DEFAULT_VC_PAGE4 0
#define GR55_DEFAULT_VC_PAGE1 PAGE_VC_GR55_PATCH_BANK
#define GR55_DEFAULT_VC_PAGE2 PAGE_VC_SY1000_SCENES
#define GR55_DEFAULT_VC_PAGE3 PAGE_VC_GR55_ASSIGNS
#define GR55_DEFAULT_VC_PAGE4 0
#define HLX_DEFAULT_VC_PAGE1 PAGE_VC_HLX_PATCH_BANK
#define HLX_DEFAULT_VC_PAGE2 PAGE_VC_HLX_PARAMETER
#define HLX_DEFAULT_VC_PAGE3 PAGE_VC_SNAPSCENE_LOOPER
#define HLX_DEFAULT_VC_PAGE4 0
#define KPA_DEFAULT_VC_PAGE1 PAGE_VC_KPA_RIG_SELECT
#define KPA_DEFAULT_VC_PAGE2 PAGE_VC_KPA_FX_CONTROL
#define KPA_DEFAULT_VC_PAGE3 0
#define KPA_DEFAULT_VC_PAGE4 0
#define KTN_DEFAULT_VC_PAGE1 PAGE_VC_KTN_PATCH_BANK
#define KTN_DEFAULT_VC_PAGE2 PAGE_VC_KTN_FX
#define KTN_DEFAULT_VC_PAGE3 0
#define KTN_DEFAULT_VC_PAGE4 0
#define M13_DEFAULT_VC_PAGE1 PAGE_VC_M13_PARAMETER
#define M13_DEFAULT_VC_PAGE2 PAGE_VC_FULL_LOOPER
#define M13_DEFAULT_VC_PAGE3 0
#define M13_DEFAULT_VC_PAGE4 0
#define VG99_DEFAULT_VC_PAGE1 PAGE_VC_CURRENT_PATCH_BANK;
#define VG99_DEFAULT_VC_PAGE2 PAGE_VC_VG99_EDIT;
#define VG99_DEFAULT_VC_PAGE3 PAGE_VC_VG99_ASSIGNS;
#define VG99_DEFAULT_VC_PAGE4 0;
#define ZG3_DEFAULT_VC_PAGE1 PAGE_VC_ZOOM_PATCH_BANK
#define ZG3_DEFAULT_VC_PAGE2 0
#define ZG3_DEFAULT_VC_PAGE3 0
#define ZG3_DEFAULT_VC_PAGE4 0
#define ZMS70_DEFAULT_VC_PAGE1 PAGE_VC_ZOOM_PATCH_BANK
#define ZMS70_DEFAULT_VC_PAGE2 0
#define ZMS70_DEFAULT_VC_PAGE3 0
#define ZMS70_DEFAULT_VC_PAGE4 0
#define SVL_DEFAULT_VC_PAGE1 PAGE_VC_CURRENT_PATCH_BANK
#define SVL_DEFAULT_VC_PAGE2 PAGE_VC_CURRENT_PARAMETER
#define SVL_DEFAULT_VC_PAGE3 0
#define SVL_DEFAULT_VC_PAGE4 0
#define SY1000_DEFAULT_VC_PAGE1 PAGE_VC_SY1000_PATCH_BANK
#define SY1000_DEFAULT_VC_PAGE2 PAGE_VC_SY1000_SCENES
#define SY1000_DEFAULT_VC_PAGE3 PAGE_VC_SY1000_ASSIGNS
#define SY1000_DEFAULT_VC_PAGE4 0
#define GM2_DEFAULT_VC_PAGE1 PAGE_VC_CURRENT_PATCH_BANK
#define GM2_DEFAULT_VC_PAGE2 PAGE_VC_CURRENT_PARAMETER
#define GM2_DEFAULT_VC_PAGE3 0
#define GM2_DEFAULT_VC_PAGE4 0
#define MG300_DEFAULT_VC_PAGE1 PAGE_VC_MG300_PATCH_BANK
#define MG300_DEFAULT_VC_PAGE2 PAGE_VC_CURRENT_PARAMETER
#define MG300_DEFAULT_VC_PAGE3 0
#define MG300_DEFAULT_VC_PAGE4 0
#define USER_DEFAULT_VC_PAGE1 PAGE_VC_USER_PATCH_BANK
#define USER_DEFAULT_VC_PAGE2 PAGE_VC_USER_PAR_BANK
#define USER_DEFAULT_VC_PAGE3 0
#define USER_DEFAULT_VC_PAGE4 0
#define PAGE_VC_DEFAULT 0
#define PAGE_VC_COMBO1 1
#define PAGE_VC_COMBO2 2
#define PAGE_VC_FUNCTIONS_TEST 3
#define PAGE_VC_GM_TEST 4
#define FIRST_FIXED_CMD_PAGE_VCMINI 201
#define FIRST_SELECTABLE_FIXED_CMD_PAGE_VCMINI 203
#define PAGE_VCMINI_MENU 201
#define PAGE_VCMINI_CURRENT_DIRECT_SELECT 202
#define PAGE_VCMINI_DEVICE_MODE 203
#define PAGE_VCMINI_PAGE_MODE 204
#define PAGE_VCMINI_CURRENT_PATCH_BANK 205
#define PAGE_VCMINI_UP_DOWN_TAP 206
#define PAGE_VCMINI_CURRENT_PARAMETER 207
#define PAGE_VCMINI_CURRENT_ASSIGN 208
#define PAGE_VCMINI_SNAPSCENE 209
#define PAGE_VCMINI_LOOPER 210
#define PAGE_VCMINI_KPA_LOOPER 211
#define PAGE_VCMINI_KTN_FX1 212
#define PAGE_VCMINI_KTN_FX2 213
#define PAGE_VCMINI_KTN_FX3 214
#define PAGE_VCMINI_KTN4_FX1 215
#define PAGE_VCMINI_KTN4_FX2 216
#define PAGE_VCMINI_KTN4_FX3 217
#define PAGE_VCMINI_MG300_FX1 218
#define PAGE_VCMINI_MG300_FX2 219
#define PAGE_VCMINI_MG300_FX3 220
#define PAGE_VCMINI_SY1000_MODE_SEL1 221
#define PAGE_VCMINI_SY1000_MODE_SEL2 222
#define PAGE_VCMINI_KPA_RIG_SELECT 223
#define PAGE_VCMINI_SONG_MODE 224
#define PAGE_VCMINI_SETLIST_SELECT 225
#define LAST_FIXED_CMD_PAGE_VCMINI 225
#define DEFAULT_VCMINI_PAGE PAGE_VCMINI_CURRENT_PATCH_BANK // The page that gets selected when a valid page number is unknown
#define FAS_DEFAULT_VCMINI_PAGE1 PAGE_VCMINI_CURRENT_PATCH_BANK
#define FAS_DEFAULT_VCMINI_PAGE2 PAGE_VCMINI_CURRENT_PARAMETER
#define FAS_DEFAULT_VCMINI_PAGE3 PAGE_VCMINI_SNAPSCENE
#define FAS_DEFAULT_VCMINI_PAGE4 0
#define GP10_DEFAULT_VCMINI_PAGE1 PAGE_VCMINI_CURRENT_PATCH_BANK
#define GP10_DEFAULT_VCMINI_PAGE2 PAGE_VCMINI_CURRENT_PARAMETER
#define GP10_DEFAULT_VCMINI_PAGE3 PAGE_VCMINI_CURRENT_ASSIGN
#define GP10_DEFAULT_VCMINI_PAGE4 0
#define GR55_DEFAULT_VCMINI_PAGE1 PAGE_VCMINI_CURRENT_PATCH_BANK
#define GR55_DEFAULT_VCMINI_PAGE2 PAGE_VCMINI_SNAPSCENE
#define GR55_DEFAULT_VCMINI_PAGE3 PAGE_VCMINI_CURRENT_ASSIGN
#define GR55_DEFAULT_VCMINI_PAGE4 0
#define HLX_DEFAULT_VCMINI_PAGE1 PAGE_VCMINI_CURRENT_PATCH_BANK
#define HLX_DEFAULT_VCMINI_PAGE2 PAGE_VCMINI_SNAPSCENE
#define HLX_DEFAULT_VCMINI_PAGE3 PAGE_VCMINI_LOOPER
#define HLX_DEFAULT_VCMINI_PAGE4 0
#define KPA_DEFAULT_VCMINI_PAGE1 PAGE_VCMINI_KPA_RIG_SELECT
#define KPA_DEFAULT_VCMINI_PAGE2 PAGE_VCMINI_CURRENT_PARAMETER
#define KPA_DEFAULT_VCMINI_PAGE3 PAGE_VCMINI_KPA_LOOPER
#define KPA_DEFAULT_VCMINI_PAGE4 0
#define KTN_DEFAULT_VCMINI_PAGE1 PAGE_VCMINI_CURRENT_PATCH_BANK
#define KTN_DEFAULT_VCMINI_PAGE2 PAGE_VCMINI_KTN4_FX1
#define KTN_DEFAULT_VCMINI_PAGE3 0
#define KTN_DEFAULT_VCMINI_PAGE4 0
#define M13_DEFAULT_VCMINI_PAGE1 PAGE_VCMINI_CURRENT_PATCH_BANK
#define M13_DEFAULT_VCMINI_PAGE2 PAGE_VCMINI_CURRENT_PARAMETER
#define M13_DEFAULT_VCMINI_PAGE3 PAGE_VCMINI_LOOPER
#define M13_DEFAULT_VCMINI_PAGE4 0
#define VG99_DEFAULT_VCMINI_PAGE1 PAGE_VCMINI_CURRENT_PATCH_BANK;  // Default value
#define VG99_DEFAULT_VCMINI_PAGE2 PAGE_VCMINI_CURRENT_ASSIGN; // Default value
#define VG99_DEFAULT_VCMINI_PAGE3 0; // Default value
#define VG99_DEFAULT_VCMINI_PAGE4 0; // Default value
#define ZG3_DEFAULT_VCMINI_PAGE1 PAGE_VCMINI_CURRENT_PATCH_BANK
#define ZG3_DEFAULT_VCMINI_PAGE2 PAGE_VCMINI_CURRENT_PARAMETER
#define ZG3_DEFAULT_VCMINI_PAGE3 0
#define ZG3_DEFAULT_VCMINI_PAGE4 0
#define ZMS70_DEFAULT_VCMINI_PAGE1 PAGE_VCMINI_CURRENT_PATCH_BANK
#define ZMS70_DEFAULT_VCMINI_PAGE2 PAGE_VCMINI_CURRENT_PARAMETER
#define ZMS70_DEFAULT_VCMINI_PAGE3 0
#define ZMS70_DEFAULT_VCMINI_PAGE4 0
#define SVL_DEFAULT_VCMINI_PAGE1 PAGE_VCMINI_CURRENT_PATCH_BANK
#define SVL_DEFAULT_VCMINI_PAGE2 PAGE_VCMINI_CURRENT_PARAMETER
#define SVL_DEFAULT_VCMINI_PAGE3 0
#define SVL_DEFAULT_VCMINI_PAGE4 0
#define SY1000_DEFAULT_VCMINI_PAGE1 PAGE_VCMINI_SY1000_MODE_SEL1
#define SY1000_DEFAULT_VCMINI_PAGE2 PAGE_VCMINI_CURRENT_PATCH_BANK
#define SY1000_DEFAULT_VCMINI_PAGE3 PAGE_VCMINI_CURRENT_ASSIGN
#define SY1000_DEFAULT_VCMINI_PAGE4 0
#define GM2_DEFAULT_VCMINI_PAGE1 PAGE_VCMINI_CURRENT_PATCH_BANK
#define GM2_DEFAULT_VCMINI_PAGE2 PAGE_VCMINI_CURRENT_PARAMETER
#define GM2_DEFAULT_VCMINI_PAGE3 0
#define GM2_DEFAULT_VCMINI_PAGE4 0
#define MG300_DEFAULT_VCMINI_PAGE1 PAGE_VCMINI_CURRENT_PATCH_BANK
#define MG300_DEFAULT_VCMINI_PAGE2 PAGE_VCMINI_MG300_FX1
#define MG300_DEFAULT_VCMINI_PAGE3 0
#define MG300_DEFAULT_VCMINI_PAGE4 0
#define USER_DEFAULT_VCMINI_PAGE1 PAGE_VCMINI_CURRENT_PATCH_BANK
#define USER_DEFAULT_VCMINI_PAGE2 PAGE_VCMINI_CURRENT_PARAMETER
#define USER_DEFAULT_VCMINI_PAGE3 0
#define USER_DEFAULT_VCMINI_PAGE4 0
#define PAGE_VCMINI_DEFAULT 0
#define PAGE_VCMINI_GM_TEST 1
#define PAGE_VCMINI_COMBO1 2
#define PAGE_VCMINI_FUNC 3
#define FIRST_FIXED_CMD_PAGE_VCTOUCH 201
#define FIRST_SELECTABLE_FIXED_CMD_PAGE_VCTOUCH 203
#define PAGE_VCTOUCH_MENU 201
#define PAGE_VCTOUCH_CURRENT_DIRECT_SELECT 202
#define PAGE_VCTOUCH_DEVICE_MODE 203
#define PAGE_VCTOUCH_PAGE_MODE 204
#define PAGE_VCTOUCH_CURRENT_PATCH_BANK 205
#define PAGE_VCTOUCH_GR55_PATCH_BANK 206
#define PAGE_VCTOUCH_ZOOM_PATCH_BANK 207
#define PAGE_VCTOUCH_CURRENT_PARAMETER 208
#define PAGE_VCTOUCH_EDIT_PARAMETER 209
#define PAGE_VCTOUCH_GP10_ASSIGNS 210
#define PAGE_VCTOUCH_GR55_ASSIGNS 211
#define PAGE_VCTOUCH_VG99_EDIT 212
#define PAGE_VCTOUCH_M13_PARAMETER 213
#define PAGE_VCTOUCH_FULL_LOOPER 214
#define PAGE_VCTOUCH_HLX_PATCH_BANK 215
#define PAGE_VCTOUCH_HLX_PARAMETER 216
#define PAGE_VCTOUCH_SNAPSCENE_LOOPER 217
#define PAGE_VCTOUCH_KTN_PATCH_BANK 218
#define PAGE_VCTOUCH_KTN_EDIT 219
#define PAGE_VCTOUCH_KTN_FX 220
#define PAGE_VCTOUCH_KPA_RIG_SELECT 221
#define PAGE_VCTOUCH_KPA_FX_CONTROL 222
#define PAGE_VCTOUCH_KPA_LOOPER 223
#define PAGE_VCTOUCH_CURRENT_ASSIGN 224
#define PAGE_VCTOUCH_SY1000_PATCH_BANK 225
#define PAGE_VCTOUCH_SY1000_ASSIGNS 226
#define PAGE_VCTOUCH_SY1000_SCENES 227
#define PAGE_VCTOUCH_MG300_PATCH_BANK 228
#define PAGE_VCTOUCH_MIDI_PC_BANK_SELECT 229
#define PAGE_VCTOUCH_SONG_MODE 230
#define PAGE_VCTOUCH_SONG_SELECT 231
#define PAGE_VCTOUCH_SETLIST_SELECT 232
#define PAGE_VCTOUCH_USER_PATCH_BANK 233
#define PAGE_VCTOUCH_USER_PAR_BANK 234
#define PAGE_VCTOUCH_USER_SCENES 235
#define LAST_FIXED_CMD_PAGE_VCTOUCH 235
#define DEFAULT_VCTOUCH_PAGE PAGE_VCTOUCH_SELECT // The page that gets selected when a valid page number is unknown
#define FAS_DEFAULT_VCTOUCH_PAGE1 PAGE_VCTOUCH_CURRENT_PATCH_BANK
#define FAS_DEFAULT_VCTOUCH_PAGE2 PAGE_VCTOUCH_CURRENT_PARAMETER
#define FAS_DEFAULT_VCTOUCH_PAGE3 PAGE_VCTOUCH_SNAPSCENE_LOOPER
#define FAS_DEFAULT_VCTOUCH_PAGE4 0
#define GP10_DEFAULT_VCTOUCH_PAGE1 PAGE_VCTOUCH_CURRENT_PATCH_BANK
#define GP10_DEFAULT_VCTOUCH_PAGE2 PAGE_VCTOUCH_CURRENT_PARAMETER
#define GP10_DEFAULT_VCTOUCH_PAGE3 PAGE_VCTOUCH_GP10_ASSIGNS
#define GP10_DEFAULT_VCTOUCH_PAGE4 0
#define GR55_DEFAULT_VCTOUCH_PAGE1 PAGE_VCTOUCH_GR55_PATCH_BANK
#define GR55_DEFAULT_VCTOUCH_PAGE2 PAGE_VCTOUCH_SY1000_SCENES
#define GR55_DEFAULT_VCTOUCH_PAGE3 PAGE_VCTOUCH_GR55_ASSIGNS
#define GR55_DEFAULT_VCTOUCH_PAGE4 0
#define HLX_DEFAULT_VCTOUCH_PAGE1 PAGE_VCTOUCH_HLX_PATCH_BANK
#define HLX_DEFAULT_VCTOUCH_PAGE2 PAGE_VCTOUCH_HLX_PARAMETER
#define HLX_DEFAULT_VCTOUCH_PAGE3 PAGE_VCTOUCH_SNAPSCENE_LOOPER
#define HLX_DEFAULT_VCTOUCH_PAGE4 0
#define KPA_DEFAULT_VCTOUCH_PAGE1 PAGE_VCTOUCH_KPA_RIG_SELECT
#define KPA_DEFAULT_VCTOUCH_PAGE2 PAGE_VCTOUCH_KPA_FX_CONTROL
#define KPA_DEFAULT_VCTOUCH_PAGE3 0
#define KPA_DEFAULT_VCTOUCH_PAGE4 0
#define KTN_DEFAULT_VCTOUCH_PAGE1 PAGE_VCTOUCH_KTN_PATCH_BANK
#define KTN_DEFAULT_VCTOUCH_PAGE2 PAGE_VCTOUCH_KTN_FX
#define KTN_DEFAULT_VCTOUCH_PAGE3 0
#define KTN_DEFAULT_VCTOUCH_PAGE4 0
#define M13_DEFAULT_VCTOUCH_PAGE1 PAGE_VCTOUCH_M13_PARAMETER
#define M13_DEFAULT_VCTOUCH_PAGE2 PAGE_VCTOUCH_FULL_LOOPER
#define M13_DEFAULT_VCTOUCH_PAGE3 0
#define M13_DEFAULT_VCTOUCH_PAGE4 0
#define VG99_DEFAULT_VCTOUCH_PAGE1 PAGE_VCTOUCH_CURRENT_PATCH_BANK;
#define VG99_DEFAULT_VCTOUCH_PAGE2 PAGE_VCTOUCH_VG99_EDIT;
#define VG99_DEFAULT_VCTOUCH_PAGE3 PAGE_VCTOUCH_CURRENT_ASSIGN;
#define VG99_DEFAULT_VCTOUCH_PAGE4 0;
#define ZG3_DEFAULT_VCTOUCH_PAGE1 PAGE_VCTOUCH_ZOOM_PATCH_BANK
#define ZG3_DEFAULT_VCTOUCH_PAGE2 0
#define ZG3_DEFAULT_VCTOUCH_PAGE3 0
#define ZG3_DEFAULT_VCTOUCH_PAGE4 0
#define ZMS70_DEFAULT_VCTOUCH_PAGE1 PAGE_VCTOUCH_ZOOM_PATCH_BANK
#define ZMS70_DEFAULT_VCTOUCH_PAGE2 0
#define ZMS70_DEFAULT_VCTOUCH_PAGE3 0
#define ZMS70_DEFAULT_VCTOUCH_PAGE4 0
#define SVL_DEFAULT_VCTOUCH_PAGE1 PAGE_VCTOUCH_CURRENT_PATCH_BANK
#define SVL_DEFAULT_VCTOUCH_PAGE2 PAGE_VCTOUCH_CURRENT_PARAMETER
#define SVL_DEFAULT_VCTOUCH_PAGE3 0
#define SVL_DEFAULT_VCTOUCH_PAGE4 0
#define SY1000_DEFAULT_VCTOUCH_PAGE1 PAGE_VCTOUCH_SY1000_PATCH_BANK
#define SY1000_DEFAULT_VCTOUCH_PAGE2 PAGE_VCTOUCH_SY1000_SCENES
#define SY1000_DEFAULT_VCTOUCH_PAGE3 PAGE_VCTOUCH_SY1000_ASSIGNS
#define SY1000_DEFAULT_VCTOUCH_PAGE4 0
#define GM2_DEFAULT_VCTOUCH_PAGE1 PAGE_VCTOUCH_CURRENT_PATCH_BANK
#define GM2_DEFAULT_VCTOUCH_PAGE2 PAGE_VCTOUCH_CURRENT_PARAMETER
#define GM2_DEFAULT_VCTOUCH_PAGE3 0
#define GM2_DEFAULT_VCTOUCH_PAGE4 0
#define MG300_DEFAULT_VCTOUCH_PAGE1 PAGE_VCTOUCH_MG300_PATCH_BANK
#define MG300_DEFAULT_VCTOUCH_PAGE2 PAGE_VCTOUCH_CURRENT_PARAMETER
#define MG300_DEFAULT_VCTOUCH_PAGE3 0
#define MG300_DEFAULT_VCTOUCH_PAGE4 0
#define USER_DEFAULT_VCTOUCH_PAGE1 PAGE_VCTOUCH_USER_PATCH_BANK
#define USER_DEFAULT_VCTOUCH_PAGE2 PAGE_VCTOUCH_USER_PAR_BANK
#define USER_DEFAULT_VCTOUCH_PAGE3 PAGE_VCTOUCH_USER_SCENES
#define USER_DEFAULT_VCTOUCH_PAGE4 0
#define PAGE_VCTOUCH_DEFAULT 0
#define PAGE_VCTOUCH_COMBO1 1
#define PAGE_VCTOUCH_COMBO2 2
#define PAGE_VCTOUCH_FUNCTIONS_TEST 3
#define PAGE_VCTOUCH_GM_TEST 4
extern QVector<Cmd_struct> Commands;
extern const QVector<Cmd_struct> VC_commands;
extern const QVector<Cmd_struct> VCmini_commands;
extern const QVector<Cmd_struct> VCtouch_commands;
extern QVector<Cmd_struct> Fixed_commands;
extern const QVector<Cmd_struct> VC_fixed_commands;
extern const QVector<Cmd_struct> VCmini_fixed_commands;
extern const QVector<Cmd_struct> VCtouch_fixed_commands;
extern int number_of_cmds;
extern int Number_of_pages;
extern uint8_t page_default;
extern uint8_t first_fixed_cmd_page;
extern uint8_t last_fixed_cmd_page;
extern const QStringList VC_switch_names;
extern const QStringList VCmini_switch_names;
extern const QStringList VCtouch_switch_names;
extern QStringList switchnames;
