sixeight7/VController_v3/Firmware/VController_v3/hardware.h

// Please read VController_v3.ino for information about the license and authors

#ifndef HARDWARE_H
#define HARDWARE_H

// This file contains all the hardware settings for the VController Production Model version 1 - modified for the Teensy 4.1
// Make sure you include this file when updating to new firmware

#define VC_NAME "V-Controller"
#define HARDWARE_VERSION 2

// Choose which configuration for the switches is chosen in Config.ino
#define CONFIG_VCONTROLLER
//#define CONFIG_VCMINI
//#define CONFIG_VCTOUCH
//#define CONFIG_CUSTOM
#define MENU_ON_INDIVIDUAL_DISPLAYS

//#define SKIP_GR55_PRESET_NAMES // Will not compile the hardcoded preset names for the preset patches - will save around 8k of space (3% on Teensy 3.2)


// Allowable i2c rates:
// I2C_RATE_100, I2C_RATE_200, I2C_RATE_300, I2C_RATE_400, I2C_RATE_600, I2C_RATE_800, I2C_RATE_1000, I2C_RATE_1200, 
// I2C_RATE_1500, I2C_RATE_1800, I2C_RATE_2000, I2C_RATE_2400, I2C_RATE_2800, I2C_RATE_3000

#define WIRE_SPEED 1000000
#define WIRE2_SPEED 1000000
#define WireLQ Wire2 // Sets the i2c port for the main display to port 3 (Wire2)

// *** Pinout of the Teensy
// If a pin is not connected in your hardware, just add a // before it.
#define POWER_PIN           4  // This pin that switches power on and off - enabling this pin enables the power on/off procedures in the code
#define POWER_SWITCH_PIN    5  // The pin that goes to the power switch - can be one of the VController top switches or an external switch
#define POWER_SWITCH_NUMBER 13 // Power switch is same as switch 13: top left switch of VController
#define INTA_PIN            2  // Digital Pin 2 of the Teensy is connected to INTA of the MCP23017 on the display boards - defining this pin enables the display boards in the code
#define NEOPIXELLEDPIN     17  // The NeoPixel LEDs are connected to pin 17.
#define BACKLIGHTNEOPIXELPIN 3 // The WS2811 chips for the backlights are connected to pin 3 - defining this pin enables the backlight procedures in the code

// Pin 15,16, 20, 21, 22, 23, 27 and 28 are used for switches. They are declared below

// *** Switches (internal)
#define NUMBER_OF_SWITCHES 16 // Number of foot switches
#define NUMBER_OF_ENCODERS 0
#define NUMBER_OF_EXTERNAL_SWITCHES 8
#define NUMBER_OF_MIDI_SWITCHES 0
#define TOTAL_NUMBER_OF_SWITCHES 24 // NUMBER_OF_SWITCHES + (NUMBER_OF_ENCODERS * 2) + NUMBER_OF_EXTERNAL_SWITCHES + NUMBER_OF_MIDI_SWITCHES

#define SWITCH_BOUNCE_TIME 100 // in ms

// If we have a switchpad, define it here
/*#define ROWS 4 //number of rows in switchpad
#define COLS 4 //number of columns in switchpad
#define ROWPINS 5, 4, 3, 2
#define COLUMNPINS 13, 12, 11, 6*/

// *** Switches and expression pedals (external)
#define NUMBER_OF_CTL_JACKS 4 // Number of jacks on the VController for connecting an expression pedal or two switches 

// Pin numbers in the Teensy (digital tip, digital ring, analog tip, analog ring, max_ring_for_exp_pedal) - make sure you write the analog pin numbers as A0 and not just 0
#define JACK1_PINS 26, 14, A12, A0, 1000
#define JACK2_PINS 15, 16, A1, A2, 1000
#define JACK3_PINS 20, 21, A6, A7, 1000
#define JACK4_PINS 22, 23, A8, A9, 1000

#define JACK_PORT_PULLUP false // There are already pull-up resistors externally

#define MENU_KEY_COMBINATION 0x9000 // Switches 13 and 16
#define YES_SWITCH 10
#define NO_SWITCH 11

// *** Neopixel LEDs
#define NUMBER_OF_LEDS     12 // Number of neopixel LEDs connected
#define LED_ORDER          0, 3, 6, 9, 1, 4, 7, 10, 2, 5, 8, 11 // The order in which the LEDs are connected

#define NUMBER_OF_BACKLIGHTS     12 // Number of WS2811 chips for backlight connected
#define BACKLIGHT_ORDER          0, 3, 6, 9, 1, 4, 7, 10, 2, 5, 8, 11 // The order in which the chips are connected


// *** Display settings of the main display - so far it is connected to a regular display board
#define PRIMARY_MAIN_DISPLAY_ADDRESS 0x3F // If we have a PCF8745AT chip in the i2c expander
#define SECONDARY_MAIN_DISPLAY_ADDRESS 0x27 // If we have a PCF8745T chip in the i2c expander
#define MAIN_LCD_DISPLAY_SIZE 16

// *** Individual displays above switches
#define NUMBER_OF_DISPLAY_BOARDS 4
#define NUMBER_OF_DISPLAYS 12
#define INDIVIDUAL_DISPLAYS
#define LCD_DISPLAY_SIZE 16

// Define the addresses and numbers of the displays using the VController display boards based on an MCP23017. Maximum 15 displays can be defined here. 
// Make sure the number of displays here matches the NUMBER_OF_DIPLAYS variable.
// You cannot declare displays both here and in the next section.

#define DISPLAY_01_ADDRESS_AND_NUMBER 0x20, DISPLAY1
#define DISPLAY_02_ADDRESS_AND_NUMBER 0x21, DISPLAY1
#define DISPLAY_03_ADDRESS_AND_NUMBER 0x22, DISPLAY1
#define DISPLAY_04_ADDRESS_AND_NUMBER 0x23, DISPLAY1
#define DISPLAY_05_ADDRESS_AND_NUMBER 0x20, DISPLAY2
#define DISPLAY_06_ADDRESS_AND_NUMBER 0x21, DISPLAY2
#define DISPLAY_07_ADDRESS_AND_NUMBER 0x22, DISPLAY2
#define DISPLAY_08_ADDRESS_AND_NUMBER 0x23, DISPLAY2
#define DISPLAY_09_ADDRESS_AND_NUMBER 0x20, DISPLAY3
#define DISPLAY_10_ADDRESS_AND_NUMBER 0x21, DISPLAY3
#define DISPLAY_11_ADDRESS_AND_NUMBER 0x22, DISPLAY3
#define DISPLAY_12_ADDRESS_AND_NUMBER 0x23, DISPLAY3


// Define the addresses of the displays using regular i2C backpacks here. Maximum 15 displays can be defined here. 
// Make sure the number of displays here matches the NUMBER_OF_DIPLAYS variable
/*
#define DISPLAY_01_ADDRESS 0x21
#define DISPLAY_02_ADDRESS 0x22
#define DISPLAY_03_ADDRESS 0x23
#define DISPLAY_04_ADDRESS 0x24
#define DISPLAY_05_ADDRESS 0x25
#define DISPLAY_06_ADDRESS 0x26
#define DISPLAY_07_ADDRESS 0x39
#define DISPLAY_08_ADDRESS 0x3A
#define DISPLAY_09_ADDRESS 0x3B
#define DISPLAY_10_ADDRESS 0x3D
#define DISPLAY_11_ADDRESS 0x20
#define DISPLAY_12_ADDRESS 0x3E
*/

// Pinout on PCF8745 i2c expanders
#define BACKLIGHT_PIN     3
#define EN_PIN  2
#define RW_PIN  1
#define RS_PIN  0
#define D4_PIN  4
#define D5_PIN  5
#define D6_PIN  6
#define D7_PIN  7

// Expansion board Raspberry Pi running VCbridge
#define LINE_SELECT_CC_NUMBER 119
#define VCONTROLLER_MIDI_CHANNEL 16

#define NUMBER_OF_MIDI_PORTS 4
#define MIDI1_SERIAL_PORT Serial1
#define MIDI2_SERIAL_PORT Serial7
#define MIDI3_SERIAL_PORT Serial2
#define MIDI3_ENABLED
//#define MIDI4_SERIAL_PORT Serial4
//#define MIDI4_ENABLED
//#define MIDI5_SERIAL_PORT Serial5
//#define MIDI5_ENABLED

// Names and numbers of ports
#define PORT1_NAME "USB MIDI"
#define PORT1_TYPE USBMIDI_PORT
#define PORT1_NUMBER 0

#define PORT2_NAME "MIDI 1"
#define PORT2_TYPE MIDI1_PORT
#define PORT2_NUMBER 1

#define PORT3_NAME "MIDI 2"
#define PORT3_TYPE MIDI2_PORT
#define PORT3_NUMBER 2

#define PORT4_NAME "INT RPI MIDI"
#define PORT4_TYPE MIDI3_PORT
#define PORT4_NUMBER 3

#define PORT5_NAME "ALL MIDI PORTS"
#define PORT5_TYPE ALL_MIDI_PORTS
#define PORT5_NUMBER 4

#define PORT6_NAME ""
#define PORT6_TYPE USBMIDI_PORT
#define PORT6_NUMBER 5

#define PORT7_NAME ""
#define PORT7_TYPE USBMIDI_PORT
#define PORT7_NUMBER 6

#define PORT8_NAME ""
#define PORT8_TYPE USBMIDI_PORT
#define PORT8_NUMBER 7

#define PORT9_NAME ""
#define PORT9_TYPE USBMIDI_PORT
#define PORT9_NUMBER 8
#endif
