sixeight7/VController_v3/Firmware/VC-edit/vccommands.h

#ifndef VCCOMMANDS_H
#define VCCOMMANDS_H

// VCcommands is the interface with the Commands[] and Fixed_commands[] arrays.
// The structure is the same as on the VController, including the indexes for both programmable and fixed commands.
// The data at the bottom of this page is the same as on the VController

#include "VController/hardware.h"
#include "VController/config.h"
#include "customlistwidget.h"
#include "VController/globals.h"
#include "VController/globaldevices.h"

#include <QObject>
#include <QComboBox>
#include <QListWidget>
#include <QTableWidget>

#define MAX_NUMBER_OF_PAGES 256
#define EXT_EEP_MAX_NUMBER_OF_COMMANDS_VC_AND_VCMINI 1737
#define EXT_EEP_MAX_NUMBER_OF_COMMANDS_VCTOUCH 3225
extern uint16_t EXT_EEP_MAX_NUMBER_OF_COMMANDS;
#define MAX_NUMBER_OF_INTERNAL_COMMANDS 1000
#define INTERNAL_CMD 0x8000 // MSB of an index set indicates the command is an internal command

#define MEMORY_FULL 0xFFFF

class VCcommands : public QObject
{
    Q_OBJECT

public:
    explicit VCcommands(QObject *parent = nullptr);
    void setup_VC_config();
    void recreate_indexes();
    // fill page widgets:
    void fillPageComboBox(QComboBox *cbox);
    void fillFixedPageComboBox(QComboBox *cbox);
    void fillSwitchComboBox(QComboBox *cbox);
    void fillCommandsListWidget(QObject *parent, customListWidget *cmdList, uint8_t pg, uint8_t sw, bool show_default_page, bool first_time);
    void fillCommandTableWidget(QTableWidget *table, uint8_t pg, uint8_t sw, int cmd);
    void updateCommandsTableWidget();
    void setCommandTabWidget(QTabWidget *tabWidget, uint8_t pg, uint8_t sw, uint8_t cmd);
    void saveCommand(uint8_t pg, uint8_t sw, uint8_t cmd);
    void checkSaved(uint8_t pg, uint8_t sw, uint8_t cmd);
    int createNewCommand(uint8_t pg, uint8_t sw);
    int deleteCommand(uint8_t pg, uint8_t sw, uint8_t item);
    QString customLabelString(uint8_t pg, uint8_t sw);
    bool setCustomLabelString(uint8_t pg, uint8_t sw, QString label);
    int valueFromIndex(uint8_t type, uint16_t index);
    int indexFromValue(uint8_t type, uint16_t pageNumber);
    void swapSwitches(int pg1, int sw1, int pg2, int sw2);
    uint8_t duplicatePage(int pg);
    void clearPage(int pg);
    int addPage();
    void readAll(const QJsonObject &json);
    void readPage(int pg, const QJsonObject &json);
    void readCommand(QJsonObject &json, int pgOverride);
    void writeAll(QJsonObject &json) const;
    void writePage(int pg, QJsonObject &json);
    void writeCommand(uint16_t cmd_no, QJsonObject &json) const;
    QString getPageName(int pg);
    QString getSwitchName(int sw) const;
    bool switchHasLabel(int pg, int sw);
    bool switchShowsDefaultItems(int pg, int sw);
    void copyItemsToBuffer(customListWidget *widget);
    void pasteItem(int sw);

signals:
    void updateCommandScreens(bool);
    void updateEditCommandScreen();
    void customContextMenuRequested(QPoint);

public slots:

    void copyCommand(customListWidget *sourceWidget, int sourceRow, customListWidget *destWidget);
    void moveCommand(customListWidget *widget, int sourceRow, int destRow);
    void cmdByteDataChanged(int, int, int);

private:
    // Low level interfacing with the command array.
    void copy_command_structure(QVector<Cmd_struct>* source, QVector<Cmd_struct>* dest, uint16_t size);
    void create_indexes();
    uint16_t new_command_index();
    void delete_cmd(uint16_t number);
    Cmd_struct get_cmd(uint16_t number);
    void write_cmd(uint16_t number, Cmd_struct &cmd);
    uint16_t get_cmd_number(uint8_t pg, uint8_t sw, uint8_t number);
    uint16_t get_cmd_number_check_default(uint8_t pg, uint8_t sw, uint8_t number);
    uint16_t count_cmds(uint8_t pg, uint8_t sw);
    QString create_cmd_string(uint16_t number);
    QString read_title(uint8_t pg, uint8_t sw);
    void write_title(uint8_t pg, uint8_t sw, QString title);

    // Low level procedures for command creation
    QString cmdTypeString(uint8_t type);
    QString cmdDeviceString(uint8_t dev);
    QString cmdSwitchTypeString(uint8_t sw);
    void set_type_and_value(uint8_t number, uint8_t type, uint8_t value, bool in_edit_mode);
    void clear_cmd_bytes(uint8_t start_byte, bool in_edit_mode);
    void build_command_structure(uint8_t cmd_byte_no, uint8_t cmd_type, bool in_edit_mode);
    void set_default_parameter_values(bool in_edit_mode);
    uint8_t current_cmd_function();
    uint8_t get_switch_trigger_number(uint8_t sw);
    uint8_t get_switch_trigger_type(uint8_t value);
    bool is_label(uint8_t sw);
    void load_cmd_byte(QTableWidget *table, uint8_t cmd_byte_no);
    QString read_cmd_sublist(uint8_t cmd_byte_no, uint16_t value);

    QTableWidget *MyTable = nullptr;
    int current_page = 0;
    int current_switch = 0;
    int current_item = 0;
    int pageDuplicateCounter = 2;
    QString addNewNumber(QString inputString);

    QVector<Cmd_struct> copyBuffer;
    QString copyBufferLabel = "";
    bool copyBufferContainsLabel = false;
    bool copyBufferFilled = false;

    customListWidget *lastWidget = 0;

    uint16_t First_cmd_index[MAX_NUMBER_OF_PAGES][NUMBER_OF_SWITCHES + NUMBER_OF_EXTERNAL_SWITCHES + 1]; // Gives the index number of every first command for every dwitch on every page
    uint16_t Next_cmd_index[EXT_EEP_MAX_NUMBER_OF_COMMANDS_VCTOUCH]; // Gives the number of the next command that needs to be read from EEPROM
    uint16_t Next_internal_cmd_index[MAX_NUMBER_OF_INTERNAL_COMMANDS]; // Gives the index of the next command that needs to be read from Fixed_commands[]
    uint16_t Title_index[MAX_NUMBER_OF_PAGES][NUMBER_OF_SWITCHES + NUMBER_OF_EXTERNAL_SWITCHES + 1]; // gives the index number of the title command for page 0 (page title) and every switch with a display
    bool isIndexed = false;

    uint8_t selected_device_cmd = PATCH - 100;
    uint8_t selected_common_cmd = PAGE;
    bool command_edited = false;
    bool commandListBoxContainsLabel = false;

    struct cmdtype_struct {
      QString Title;
      uint8_t Sublist;
      uint8_t Min;
      uint8_t Max;
    };

    #define TYPE_OFF 0
    #define TYPE_DEVICE_SELECT 1
    #define TYPE_COMMON_COMMANDS 2
    #define TYPE_DEVICE_COMMANDS 3
    #define TYPE_PAGE 4
    #define TYPE_CMDTYPE 5
    #define TYPE_MIDI_PORT 6
    #define TYPE_MIDI_CHANNEL 7
    #define TYPE_CC_NUMBER 8
    #define TYPE_CC_TOGGLE 9
    #define TYPE_VALUE 10
    #define TYPE_NOTE_NUMBER 11
    #define TYPE_NOTE_VELOCITY 12
    #define TYPE_PC 13
    #define TYPE_REL_NUMBER 14
    #define TYPE_BANK_SIZE 15
    #define TYPE_PATCH_NUMBER 16
    #define TYPE_PATCH_100 17
    #define TYPE_PARAMETER 18
    #define TYPE_PAR_VALUE 19
    #define TYPE_ASSIGN 20
    #define TYPE_ASSIGN_TRIGGER 21
    #define TYPE_TOGGLE 22
    #define TYPE_STEP 23
    #define TYPE_SWITCH_TRIGGER 24
    #define TYPE_SWITCH 25
    #define TYPE_CMD 26
    #define TYPE_BPM 27
    #define TYPE_MIN 28
    #define TYPE_MAX 29
    #define TYPE_SNAPSCENE 30
    #define TYPE_LOOPER 31
    #define TYPE_EXP_PEDAL 32
    #define TYPE_CMDTYPE_ASSIGN 33
    #define TYPE_SETLIST 34
    #define TYPE_SETLIST_TYPE 35
    #define TYPE_SONG 36
    #define TYPE_SONG_TYPE 37
    #define TYPE_SONGPART 38
    #define TYPE_SONGPREVNEXT 39
    #define TYPE_MODE 40
    #define TYPE_MIDI_MORE 41
    #define TYPE_MUTE 42

    // Some of the data for the sublists below is not fixed, but must be read from a Device class or from EEPROM
    // Here we define these sublists
    #define SUBLIST_PATCH 255 // To show the patchnumber
    #define SUBLIST_PARAMETER 254 // To show the parameter name
    #define SUBLIST_PAR_VALUE 253 // To show the parameter state
    #define SUBLIST_ASSIGN 252 // To show the assign name
    #define SUBLIST_TRIGGER 251 // To show the assign trigger
    #define SUBLIST_PAGE 250 // To show the page name
    #define SUBLIST_CMD 249 // To show the selected command
    #define SUBLIST_DEVICES 248 // To show the devices + Current and Common
    #define SUBLIST_PATCH_BANK 247
    #define SUBLIST_SWITCH 246
    #define SUBLIST_MIDI_PORT 245
    #define SUBLIST_SETLIST 244 // To show the setlist name
    #define SUBLIST_SONG 243 // To show the song name

    #define SWITCH_MAX_NUMBER 24


    const QVector<cmdtype_struct> cmdtype = {
        { "", 0, 0, 0 }, // TYPE_OFF 0
        { "DEVICE", SUBLIST_DEVICES, 0, (NUMBER_OF_DEVICES + 1) }, // TYPE_DEVICE_SELECT 1
        { "COMMAND", 1, 0, NUMBER_OF_COMMON_TYPES - 1 }, // TYPE_COMMON_COMMANDS 2
        { "COMMAND", 18, 0, NUMBER_OF_DEVICE_TYPES - 1 }, // TYPE_DEVICE_COMMANDS 3
        { "PAGE", SUBLIST_PAGE, 0, last_fixed_cmd_page }, // TYPE_PAGE 4
        { "SELECT TYPE", 129, 0, NUMBER_OF_SELECT_TYPES - 1 }, // TYPE_CMDTYPE 5
        { "MIDI PORT", SUBLIST_MIDI_PORT, 0, number_of_midi_ports }, // TYPE_MIDI_PORT 6
        { "MIDI CHANNEL", 0, 1, 16 }, // TYPE_MIDI_CHANNEL 7
        { "CC NUMBER", 0, 0, 127 }, // TYPE_CC_NUMBER 8
        { "CC TOGGLE TYPE", 85, 0, 6 }, // TYPE_CC_TOGGLE 9
        { "VALUE", 0, 0, 127 }, // TYPE_VALUE 10
        { "NOTE NUMBER", 0, 0, 127 }, // NOTE_NUMBER 11
        { "NOTE VELOCITY", 0, 0, 127 }, // TYPE_NOTE_VELOCITY 12
        { "PROGRAM", 0, 0, 127 }, // TYPE_PC 13
        { "NUMBER", 0, 1, 16 }, // TYPE_REL_NUMBER 14
        { "BANK SIZE", 0, 1, 16 }, // TYPE_BANK_SIZE 15
        { "PATCH NUMBER", SUBLIST_PATCH, 0, 99 }, // TYPE_PATCH_NUMBER 16
        { "PATCH BANK (100)", SUBLIST_PATCH_BANK, 0, 255 }, // TYPE_PATCH_100 17
        { "PARAMETER", SUBLIST_PARAMETER, 0, 255 }, // TYPE_PARAMETER 18
        { "VALUE", SUBLIST_PAR_VALUE, 0, 255 }, // TYPE_PAR_VALUE 19
        { "ASSIGN", SUBLIST_ASSIGN, 0, 255 }, // TYPE_ASSIGN 20
        { "TRIGGER", SUBLIST_TRIGGER, 1, 127 }, // TYPE_ASSIGN 21
        { "TOGGLE TYPE", 50, 0, 7 }, // TYPE_TOGGLE 22
        { "STEP", 0, 1, 127 }, // TYPE_STEP 24
        { "SWITCH TRIGGER", 111, 0, 5 }, // TYPE_SWITCH_TRIGGER 24
        { "SWITCH", SUBLIST_SWITCH, 0, SWITCH_MAX_NUMBER }, // TYPE_SWITCH 25
        { "COMMAND", SUBLIST_CMD, 0, 255 }, // TYPE_CMD 26
        { "BPM", 0, 40, 250 }, // TYPE_BPM 27
        { "MIN", 0, 0, 127 }, // TYPE_MIN 28
        { "MAX", 0, 0, 127 }, // TYPE_MAX 29
        { "SNAPSHOT/SCENE", 0, 0, 8 }, // TYPE_SNAPSCENE 30
        { "LOOPER", 92, 0, 10 }, // TYPE_LOOPER 31
        { "EXP.PEDAL", 103, 0, 3 }, // TYPE_EXP_PEDAL 32
        { "SELECT TYPE", 129, 0, 3 }, // TYPE_CMDTYPE_ASSIGN 33
        { "SETLIST", SUBLIST_SETLIST, 0, MAX_NUMBER_OF_SETLISTS }, // TYPE_SETLIST 34
        { "SELECT TYPE", 137, 0, 6 }, // TYPE_SETLIST_TYPE 35
        { "SONG", SUBLIST_SONG, 0, MAX_NUMBER_OF_SONGS }, // TYPE_SONG 36
        { "SELECT TYPE", 145, 0, 7 }, // TYPE_SONG_TYPE 37
        { "SONG PART", 0, 0, 7 }, // TYPE_SONGPART 38
        { "INC/DEC TYPE", 154, 0, 2 }, // TYPE_SONGPREVNEXT 39
        { "MODE", 157, 0, 2 }, // TYPE_MODE
        { "COMMAND", 160, 0, 2 }, // TYPE_MIDI_MORE
        { "MUTE TYPE", 163, 0, 3 }, // TYPE_MUTE
    };

    const QStringList cmd_sublist = {

        // Sublist 1 - 17: Common Command Types
        "NO COMMAND", "PAGE", "TAP TEMPO", "SET TEMPO", "GLOBAL TUNER", "MIDI PC", "MIDI CC", "MIDI NOTE", "NEXT DEVICE", "SETLIST", "SONG", "MODE", "MIDI MORE", "MENU", "", "", "",

        // Sublist 18 - 39: Device Command Types
        "PATCH", "PARAMETER", "ASSIGN", "SNAP/SCENE", "LOOPER", "MUTE", "SEL DEVICE PAGE", "SEL NEXT PAGE", "MASTER EXP PEDAL", "TOGGL MASTER EXP",
        "DIR.SELECT", "PAR BANK", "PAR BANK UP", "PAR BANK DOWN", "PARBANK_CATEGORY", "SAVE PATCH", "", "", "", "", "", "",

        // Sublist 40 - 49: MIDI ports
        "OFF", MIDI_PORT_NAMES,

        // Sublist 50 - 59: Toggle types
        "MOMENTARY", "TOGGLE", "TRISTATE", "FOURSTATE", "STEP",  "RANGE",  "UPDOWN", "ONE SHOT", "", "",

        // Sublist 60 - 84: Switch types
        "On Page Select", "Switch 1", "Switch 2", "Switch 3", "Switch 4", "Switch 5", "Switch 6", "Switch 7", "Switch 8",
        "Switch 9", "Switch 10", "Switch 11", "Switch 12", "Switch 13", "Switch 14", "Switch 15", "Switch 16",
        "Ext 1 / Exp1", "Ext 2", "Ext 3 / Exp 2", "Ext 4", "Ext 5 / Exp 3", "Ext 6", "Ext 7 / Exp 4", "Ext 8",

        // Sublist 85 - 91: CC toggle types
        "ONE SHOT", "MOMENTARY", "TOGGLE", "TOGGLE ON", "RANGE", "STEP", "UPDOWN",

        // Sublist 92 - 102: CC toggle types
        "OFF", "ON/OFF", "PLAY/STOP", "REC/OVERDUB", "UNDO/REDO", "HALF SPEED", "REVERSE", "PLAY ONCE", "PRE/POST", "REC/PLAY/OVERDUB", "STOP/ERASE",

        // Sublist 103 - 110: EXP pedal types
        "TOGGLE", "EXP1", "EXP2", "EXP3", "", "", "", "",

        // Sublist 111 - 117: Command switch trigger types
        "ON PRESS", "ON RELEASE", "ON LONG PRESS", "ON DUAL PRESS", "ON DUAL RELEASE", "ON DUAL LONG PRS", "", "",

        // Sublist 118 - 128
        "On Page Select", "Switch 1", "Switch 2", "Switch 3", "Rotary 1", "Rotary Switch 1", "Rotary 2", "Rotary Switch 2", "Ext1 / Exp", "Ext 2",

        // Sublist 129 - 136 Page/ patch select types
        "SELECT", "BANK SELECT", "BANK UP", "BANK DOWN", "NEXT", "PREVIOUS", "", "",

        // Sublist 137 - 144: Setlist select types
        "SELECT", "BANK SELECT", "BANK UP", "BANK DOWN", "NEXT", "PREVIOUS", "EDIT", "",

        // Sublist 145 - 154: Song select types
        "SELECT", "BANK SELECT", "BANK UP", "BANK DOWN", "NEXT", "PREVIOUS", "PARTSEL", "EDIT", "",

        // Sublist 154 - 156: Song inc/dec types
        "SONG", "PART", "SONG+PART",

        // Sublist 157 - 159: Mode types
        "SONG", "PAGE", "DEVICE",

        // Sublist 160 - 162: Midi more types
        "START", "STOP", "START/STOP",

        // Sublist 163 - 166: Mute types
        "ON", "OFF", "OFF/ALWAYS ON", "TOGGLE",
    };

#define INDEX_PAR_TOGGLE_TYPE 50
#define INDEX_CC_TOGGLE_TYPE 85

    struct cmdbyte_struct {
      uint8_t Type;
      QString Title;
      uint16_t Value;
      uint16_t Min;
      uint16_t Max;
    };

    #define CB_SWITCH_TRIGGER 0
    #define CB_DEVICE 1
    #define CB_TYPE 2
    #define CB_DATA1 3
    #define CB_DATA2 4
    #define CB_VAL1 5
    #define CB_VAL2 6
    #define CB_VAL3 7
    #define CB_VAL4 8
    #define CB_PAGE 9
    #define CB_SWITCH 10
    #define CB_CMD_NO 11

    #define NUMBER_OF_CMD_BYTES 9

    cmdbyte_struct cmdbyte[NUMBER_OF_CMD_BYTES] = {
      // Default command to edit
        { TYPE_SWITCH_TRIGGER, "SWITCH TRIGGER", 0, 0, 6 }, // CB_SWITCH_TRIGGER
        { TYPE_DEVICE_SELECT, "DEVICE", (NUMBER_OF_DEVICES + 1), 0, (NUMBER_OF_DEVICES + 1) },
        { TYPE_COMMON_COMMANDS, "COMMAND", 0, 0, NUMBER_OF_COMMON_TYPES},
        { TYPE_OFF, "", 0, 0, 0},
        { TYPE_OFF, "", 0, 0, 0},
        { TYPE_OFF, "", 0, 0, 0},
        { TYPE_OFF, "", 0, 0, 0},
        { TYPE_OFF, "", 0, 0, 0},
        { TYPE_OFF, "", 0, 0, 0},
    };

    uint8_t Cmd_switch_trigger = 0;
};

#endif // VCCOMMANDS_H
