sixeight7/VController_v3/Firmware/VController_v3/Class_MD.ino

// Please read VController_v3.ino for information about the license and authors

// This page has the following parts:
// Section 1: MD_base_class declaration (base)
// Section 2: MD_GP10_class declaration (derived)
// Section 3: MD_GR55_class declaration (derived)
// Section 4: MD_VG99_class declaration (derived)
// Section 5: MD_ZG3_class declaration (derived)
// Section 6: MD_ZMS_class declaration (derived)
// Section 7: MD_M13_class declaration (derived)
// Section 8: MD_HLX_class declaration (derived)
// Section 9: MD_FAS_class declaration (derived)
// Section 10: MD_KTN_class declaration (derived)
// Section 11: MD_KPA_class declaration (derived)
// Section 12: MD_SVL_class declaration (derived)
// Section 13: MD_SY1000_class declaration (derived)
// Section 14: MD_GM2_class declaration (derived)
// Section 15: MD_MG300_class declaration (derived)
// Section 16: MD_USER_class declaration (derived)

// Here we declare the class objects for the midi devices the VController supports. The actual class code is found in the Md_<device_name>.ino files.

// We use a derived class structure here.
// The base class is MD_base_class. For each device there is a derived class, where certain functions are replaced to add device specific functionality.
// For a derived function to work, "virtual" must be declared in the header of the base class! I have forgotten this a number of times, so this is a reminder to self!
//#include <util/crc16.h>
#define VC_PATCH_SIZE 192 // The size of a patch for Katana or SY1000

// ********************************* Section 1: MD_base_class declaration (base) ********************************************

#define NUMBER_OF_DEVICE_SETTINGS 12

class MD_base_class
{ // Base class for midi devices

  public:
    // Procedures:
    MD_base_class (uint8_t _dev_no); // Constructor

    // Basic procedures
    virtual void init(); // Called in setup() of sketch
    virtual void update(); // Called in loop() of sketch
    uint8_t get_setting(uint8_t variable);
    void set_setting(uint8_t variable, uint8_t value);
    virtual uint8_t get_number_of_dev_types();
    virtual void get_dev_type_name(uint8_t number, String &name);
    virtual void do_after_dev_type_update();

    // Midi in procedures
    virtual void check_SYSEX_in(const unsigned char* sxdata, short unsigned int sxlength, uint8_t port);
    virtual void forward_MIDI_message(const unsigned char* sxdata, short unsigned int sxlength);
    virtual void check_PC_in(uint8_t program, uint8_t channel, uint8_t port);
    virtual void forward_PC_message(uint8_t program, uint8_t channel);
    virtual void check_CC_in(uint8_t control, uint8_t value, uint8_t channel, uint8_t port);
    virtual void check_active_sense_in(uint8_t port);
    void set_patch_number(uint16_t number);

    // Device connection procedures
    virtual void check_still_connected();
    void check_manual_connection();
    virtual bool can_request_sysex_data();
    virtual void send_alternative_identity_request(uint8_t check_device_no);
    virtual void identity_check(const unsigned char* sxdata, short unsigned int sxlength, uint8_t in_port, uint8_t out_port);
    void connect(uint8_t device_id, uint8_t in_port, uint8_t out_port);
    virtual void do_after_connect();
    void disconnect();
    virtual void do_after_disconnect();

    // Midi out procedures
    void check_sysex_delay();
    uint8_t calc_Roland_checksum(uint16_t sum);
    virtual void set_bpm();
    virtual void bpm_tap();
    virtual void start_tuner();
    virtual void stop_tuner();

    // Patch selection procedures
    virtual void select_patch(uint16_t new_patch);
    virtual void do_after_patch_selection();
    //virtual uint32_t  calculate_patch_address(uint16_t number);
    virtual bool request_patch_name(uint8_t sw, uint16_t number);
    virtual void request_current_patch_name();
    uint16_t calculate_patch_number(uint8_t bank_position, uint8_t bank_size);
    bool patch_select_pressed(uint16_t new_patch, uint8_t sw);
    uint16_t calculate_prev_next_patch_number(signed int delta);
    void bank_updown(signed int delta, uint8_t my_bank_size);
    bool bank_selection_active();
    void update_bank_number(uint16_t number);
    void update_bank_size(uint8_t b_size);
    virtual bool flash_LEDs_for_patch_bank_switch(uint8_t sw);
    void display_patch_number_string();
    virtual void number_format(uint16_t number, String &Output);
    void build_patch_number(uint16_t number, String &Output, String firstPatch, String lastPatch);
    uint8_t convert_mask_number(char c);

    uint16_t get_patch_min();
    uint16_t get_patch_max();

    // Setlist/song select
    virtual void setlist_song_select(uint16_t item);
    virtual uint16_t setlist_song_get_current_item_state();
    virtual uint16_t setlist_song_get_number_of_items();
    virtual void setlist_song_full_item_format(uint16_t item, String &Output);
    virtual void setlist_song_short_item_format(uint16_t item, String &Output);
    uint16_t patch_number_in_current_setlist(uint16_t number);

    // Direct select procedures
    virtual void direct_select_format(uint16_t number, String &Output);
    virtual bool valid_direct_select_switch(uint8_t number);
    virtual void direct_select_start();
    virtual uint16_t direct_select_patch_number_to_request(uint8_t number);
    virtual void direct_select_press(uint8_t number);

    // Device mute procedures
    virtual void unmute();
    virtual void mute();
    void check_for_mute();
    void select_switch();
    void is_always_on_toggle();
    bool US20_mode_enabled();

    // Parameter control procedures
    virtual void read_parameter_title(uint16_t number, String &Output);
    virtual void read_parameter_title_short(uint16_t number, String &Output);
    virtual void read_parameter_name(uint16_t number, String &Output);
    virtual void read_parameter_value_name(uint16_t number, uint16_t value, String &Output);
    virtual void parameter_press(uint8_t Sw, Cmd_struct *cmd, uint16_t number);
    virtual void parameter_release(uint8_t Sw, Cmd_struct *cmd, uint16_t number);
    virtual bool request_parameter(uint8_t sw, uint16_t number);
    virtual uint16_t number_of_parameters();
    virtual uint8_t number_of_values(uint16_t parameter);
    virtual uint16_t number_of_parbank_parameters();
    virtual uint16_t get_parbank_parameter_id(uint16_t par_number);
    virtual void request_par_bank_category_name(uint8_t sw);
    virtual void select_parameter_bank_category(uint8_t category);
    virtual void par_bank_updown(signed int delta, uint8_t my_bank_size);

    // Assign control procedures
    virtual void read_assign_name(uint8_t number, String &Output);
    virtual void read_assign_short_name(uint8_t number, String &Output);
    virtual void read_assign_trigger(uint8_t number, String &Output);
    virtual uint8_t get_number_of_assigns();
    virtual uint8_t trigger_follow_assign(uint8_t number);
    virtual void assign_press(uint8_t Sw, uint8_t value);
    virtual void assign_release(uint8_t Sw);
    virtual void assign_load(uint8_t sw, uint8_t assign_number, uint8_t cc_number);
    virtual void request_current_assign(uint8_t sw);
    void asgn_bank_updown(signed int delta, uint8_t my_bank_size);

    virtual void FX_press(uint8_t Sw, Cmd_struct *cmd, uint8_t number);
    virtual void FX_set_type_and_state(uint8_t Sw);

    // Master expression pedal procedures
    virtual void move_expression_pedal(uint8_t sw, uint8_t value, uint8_t exp_pedal);
    virtual void toggle_expression_pedal(uint8_t sw);
    virtual void set_expr_title(uint8_t sw);
    virtual bool request_exp_pedal(uint8_t sw, uint8_t exp_pedal);

    // Page selection procedures
    uint8_t read_current_device_page();
    uint8_t select_next_device_page();

    // Snapshot/sceme selection procedures
    virtual void get_snapscene_title(uint8_t number, String &Output);
    virtual void get_snapscene_title_short(uint8_t number, String &Output);
    virtual void get_snapscene_label(uint8_t number, String &Output);
    virtual bool request_snapscene_name(uint8_t sw, uint8_t sw1, uint8_t sw2, uint8_t sw3);
    virtual void set_snapscene(uint8_t sw, uint8_t number);
    virtual void release_snapscene(uint8_t sw, uint8_t number);
    virtual void show_snapscene(uint8_t number);
    virtual void snapscene_number_format(String &Output);
    virtual bool check_snapscene_active(uint8_t scene);
    virtual uint8_t get_number_of_snapscenes();

    // Looper procedures
    virtual bool looper_active();
    uint8_t show_looper_LED(uint8_t sw);
    uint8_t request_looper_backlight_colour();
    virtual void request_looper_label(uint8_t sw);
    void looper_press(uint8_t looper_cmd, bool send_cmd);
    virtual void looper_release();
    void looper_reset();
    void looper_timer_check();
    virtual bool send_looper_cmd(uint8_t cmd);
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
